amowry/WARBL2/warbl2_firmware/Battery_management.ino

/*
Notes:

The battery is a 400 mAH 2/3 AAA NiMH cell. Example brands are PKCell, Kastar, Dantona, and GP. Either flat top or button top works. The real-world capacity of these is usually around 350 mAH, and charging takes 3 hours.
The BQ25172 charger will charge safely without any of this code when enabled by driving the chargeEnable pin high. The code monitors the battery level and does a better job of charge termination (0 dV/dt algorithm) to prolong battery life.
The charger will only start charging if the battery voltage is below ~ 1.35V and the battery temperature is between ~ 0 and 40 degrees C.
Charging is set by resistors to ~110 mA (0.275 C) with a 4-hr safety timer. The charger will also terminate if battery voltage is > 1.7 V or battery temperature is over 40 degrees C.
Total device consumption is < 100 mA @ 5V, so any USB host (including iOS) will be able to charge.
The charger will report a fault (missing battery, out of temperature range) by blinking the STAT pin at 1 Hz.
*/

//#define PRINT_CHARGING_DATA  // For plotting voltage while charging


void manageBattery(bool send) {

    static byte chargingStatus = 0;          // 0 is not charging, 1 is charging, 2 is fault
    static byte prevChargingStatus = 0;      // Keep track of when it has changed.
    static byte tempChargingStatus;          // The assumed charging status before it has been finalized by waiting to detect a fault
    static byte prevTempChargingStatus = 0;  // Keep track of when it has changed.
    static bool chargeEnabled = false;       // Whether the charger is currently powered (by enabling the buck converter). The charger will then decide whether to charge, and report status on the STAT pin.
    static float voltageQueue[21];           // FIFO queue for finding the slope of the voltage curve while charging.
    static float voltageSlope;               // Change in smoothed voltage over the previous 10 minutes
    static unsigned long minuteTimer = 0;    // Resets every minute while charging to recalculate battery percentage.
    static bool chargeTerminated = false;    // Tells us that a charge cycle has been terminated because the cell is full.
    static byte flatSlopeCounts = 0;         // Tally of zero-slope readings (two are required to terminate charging).
    static bool statusChanged;               // Flag when the charging status has changed.
    unsigned long nowtime = millis();

    USBstatus = nrf_power_usbregstatus_vbusdet_get(NRF_POWER) + tud_ready();  // A combination of usbregstatus and tud_ready() can be used to detect battery power (0), dumb charger (1), or connected USB host (2).
    static byte prevUSBstatus;
    static unsigned long USBstatusChangeTimer;

    if (USBstatus != prevUSBstatus) {  // Keep track of when USB status changed, because we need to wait a bit for doing some things like enabling charging. USB power may be detected slightly before a USB host, causing us to briefly think there's a dumb charger.
        USBstatusChangeTimer = nowtime;
        prevUSBstatus = USBstatus;
    }

    // Check if we've been plugged in to power.
    if (battPower && USBstatus != BATTERY_POWER) {
        digitalWrite(powerEnable, LOW);  // Disable the boost converter if there is USB power. The device will then power down if USB is unplugged again.
        battPower = false;
        recordRuntime(false);  // Record how long we were under battery power.
    }


    smoothed_voltage = getBattVoltage();  // Read the battery


    // Detect charging status based on the STAT pin from the charger (off if charging, blinking if fault)
    if (!battPower) {  // Don't bother with any of this if we're not plugged in.

        // Monitor the STAT pin to tell if we're charging.
        if (digitalRead(STAT) == 0) {  // Charging
            pulseLED[RED_LED] = true;
            tempChargingStatus = 1;  // Provisionally change the status.
        } else {                     // Not charging
            pulseLED[RED_LED] = false;
            tempChargingStatus = 0;  // Provisionally change the status.
        }


        // Detect change in charging status
        if (prevTempChargingStatus != tempChargingStatus) {
            statusChanged = 1;
            if (communicationMode) {  // Send the status to the Config Tool if it has changed.
                sendMIDICouplet(MIDI_SEND_BATTERY_CHARGE_STATUS, tempChargingStatus);
            }
            prevTempChargingStatus = tempChargingStatus;
        }


        byte finalizeStatus = faultDetect(statusChanged);  // Watch for a blinking charger STAT pin, indicating a fault.
        statusChanged = 0;

        // Do nothing if finalizeStatus == 0 because there hasn't been a change or we haven't waited long enough to detect a fault.

        if (finalizeStatus == 1) {  // It's okay to accept the change in status.
            chargingStatus = tempChargingStatus;
        } else if (finalizeStatus == 2) {  // Fault
            chargingStatus = 2;
        }

        if (prevChargingStatus != chargingStatus) {
            if (chargingStatus == 1) {
                chargeStartTime = nowtime;  // Start a timer if we just started charging.
                minuteTimer = nowtime;
                for (byte i = 0; i < 21; i++) {  // Reset the readings in the voltage buffer to 0 in case there are readings in it from a previous charge cycle.
                    voltageQueue[i] = 0;
                }
                flatSlopeCounts = 0;  // Reset the number of zero-slope readings.
            }
            // Don't do anything if the charging status just changed to 0, because that means that charging was stopped by the charger, which should be rare (i.e. we missed termination and the safety timer ran down).

            prevChargingStatus = chargingStatus;

            sendMIDICouplet(MIDI_SEND_BATTERY_CHARGE_STATUS, chargingStatus);  // Send charging status again in case a fault was detected.
        }
    }




    // Estimate the battery percentage remaining via coulometry. This is a rough estimate and mostly meaningless before the first full charge because we don't know the initial state of the battery. It becomes still more accurate after the first full discharge.

    // If we're charging, every minute subtract the estimated added run time due to charging from the stored run time on the current charge (increasing the battery percentage as we're charging)
    if (chargingStatus == 1 && (nowtime - minuteTimer) > 60000) {
        prevRunTime = prevRunTime - (fullRunTime * 0.0055);  // Subtract the estimated run time added per one minute of charging.
        if (prevRunTime < 1) {
            prevRunTime = 1;  // Never go below 1.
        }

        minuteTimer = nowtime;
        static byte computeCycles = 0;
        computeCycles++;
        if (computeCycles == 5) {  // Every 5 minutes, update the recorded run time in EEPROM in case the power is cut. The EEPROM can handle more than 4 million write cycles, but don't do this too often. An EEPROM write also takes up to 5 ms.
            writeEEPROM(EEPROM_RUNTIME_START, highByte(prevRunTime));
            writeEEPROM(EEPROM_RUNTIME_START + 1, lowByte(prevRunTime));
            computeCycles = 0;
        }
    }




    // Calculate the current battery percentage based on the run time and the run time available from a full charge. Don't let it drop below 1% because if it's truly 0 it will shut down.
    unsigned long currentRun = (nowtime - runTimer) / 60000;  // Minutes we've been running since powerup

    if (!battPower) {  // Ignore time since powerup if we're plugged in.
        currentRun = 0;
    }
    battLevel = constrain(((fullRunTime - (prevRunTime + currentRun)) / float(fullRunTime)) * 100, 1, 100);  // Calculate percentage remaining.
    if ((prevRunTime + currentRun) > fullRunTime) {                                                          // If we've run longer than the expected total run time, just set the battery level to 1% until the voltage drops low enough to power down.
        battLevel = 1;
    }
    if (chargingStatus == 1 && battLevel > 98) {  // Don't let the percentage reach 100% while charging until there is a termination.
        battLevel = 98;
    }



    static byte cycles = 40;  // 40 cycles is 30 seconds.
    // Send voltage and charging status to Config Tool. This also tells the Config Tool to stay connected because it's the only message sent at a regular interval.
    if (cycles == 40 || send) {
        if (communicationMode) {
            sendMIDICouplet(MIDI_SEND_BATTERY_VOLTAGE, (((smoothed_voltage + 0.005) * 100) - 50));  // Convert to 0-127 for sending to Config Tool as 7 bits (possible range of 0.5 - 1.77 V in this format).
            sendMIDICouplet(MIDI_SEND_BATTERY_CHARGE_STATUS, chargingStatus);                       // Send charging status.
            sendMIDICouplet(MIDI_SEND_BATTERY_CHARGE_PERC, battLevel);                              // Send battery level.
        }
    }



    // If we're charging, try to detect a full cell earlier than the charger timeout by monitoring dV/dt.
    if (cycles == 40) {  // Every 30 seconds, record a new smoothed voltage reading, add it to the queue, and find the difference between the first and last reading in the queue.
        cycles = 0;

        if (chargingStatus == 1) {
            for (byte i = 0; i < 20; i++) {  // Shift a new smoothed voltage reading into the queue.
                voltageQueue[20 - i] = voltageQueue[(20 - i) - 1];
            }
            voltageQueue[0] = smoothed_voltage;

            // On rare occasions the battery voltage may suddenly jump up or down while charging. Currently undiagnosed-- it may be the charger or a change in battery load. The block below detects a sudden drop in voltage and adjusts previous measurements accordingly to prevent false termination.
            float voltageDrop = voltageQueue[1] - voltageQueue[0];
            if (voltageDrop > 0.002) {
                for (byte i = 1; i < 21; i++) {  // Adjust all previous measurements.
                    voltageQueue[i] = voltageQueue[i] - voltageDrop;
                }
                writeEEPROM(EEPROM_RESERVED_TESTING, readEEPROM(EEPROM_RESERVED_TESTING) + 1);  // Testing--record if there's been an adjustment
            }


            voltageSlope = voltageQueue[0] - voltageQueue[20];  // Find the difference in voltage over the past ten minutes (this number will be large and meaningless until 10 minutes has past and the queue has been populated--that's okay because we don't need to terminate in the first 10 minutes anyway).
            if (voltageSlope < 0.001) {                         // If the curve has been flat for the previous 10 minutes, increment the number of zero-slope readings.
                flatSlopeCounts++;
            }
            if (flatSlopeCounts >= 2) {           // If we've had two readings where the slope has been flat for the previous ten minutes, terminate charging.
                digitalWrite(chargeEnable, LOW);  // Disable charging.
                chargeEnabled = 0;
                chargeTerminated = 1;  // This tells us not to enable charging again until the power is cycled.
                //Serial.println("charge terminated by 0 dV");
                analogWrite(LEDpins[GREEN_LED], 1023);     // Indicate end of charge.
                writeEEPROM(EEPROM_RUNTIME_START, 0);      // Reset the total run time because we are now fully charged (high byte).
                writeEEPROM(EEPROM_RUNTIME_START + 1, 0);  // Low byte
                writeEEPROM(EEPROM_LOW_CHARGE, 3);         // Remember that there has been a termination.
                prevRunTime = 0;
                flatSlopeCounts = 0;
            }


#if defined(PRINT_CHARGING_DATA)
            Serial.print(smoothed_voltage, 3);
            Serial.print(",");
            Serial.print(voltageSlope, 3);
            Serial.print(",");
            Serial.println(readEEPROM(EEPROM_RESERVED_TESTING));
#endif
        }
    }

    if (!send) {  // Increment the counter if we haven't only come here to send data to the Config Tool.
        cycles++;
    }



    // Enable or disable charging (by supplying power to the charger with the buck converter) based on settings and whether USB power is available.
    // Make sure chargeEnable doesn't go high when there's no USB power because it may backpower the buck converter through the EN pin.
    if ((nowtime - USBstatusChangeTimer) > 2000 && !chargeTerminated && !chargeEnabled && ((WARBL2settings[CHARGE_FROM_HOST] && !battPower) || USBstatus == DUMB_CHARGER)) {
        digitalWrite(chargeEnable, HIGH);  // Enable charging (the charger will determine if it should actually start charging, based on batt voltage and temp.)
        chargeEnabled = 1;
        chargeStartTime = millis();
        writeEEPROM(EEPROM_RESERVED_TESTING, 0);
        if (prevRunTime > fullRunTime) {  // If we've run longer than expected on battery, make the run time the same as the expected run time when we start charging. This will allow the battery percentage to start increasing right away rather than being stuck at 1% for a while.
            prevRunTime = fullRunTime;
        }
    } else if (chargeEnabled && ((WARBL2settings[CHARGE_FROM_HOST] == 0 && USBstatus != DUMB_CHARGER) || battPower)) {  // Disable charging if we're on battery power or connected to a host and host charging isn't allowed.
        digitalWrite(chargeEnable, LOW);                                                                                // Disable charging.
        chargeEnabled = 0;
    }


    // Check to see if we've been idle long enough to power down.
    if (battPower && (nowtime - powerDownTimer > WARBL2settings[POWERDOWN_TIME] * 60000) && (WARBL2settings[POWERDOWN_TIME] < 25)) {
        powerDown(false);  // This line can be commented out to disable auto power off, for testing the battery.
    }


    // Shut down when the battery is low.
    if (nowtime > 2000 && battPower && smoothed_voltage <= 1.0) {  // Give some time to make sure we detect USB power if it's present.
        analogWrite(LEDpins[RED_LED], 1023);                       // Long red LED to indicate shutdown because of low battery
        delay(5000);
        powerDown(true);  // Power down and reset the total run time available on a full charge (because we have just measured it by using up a full charge). ToDo: Decide if the run time should only be reset if there hasn't been a partial charge during the run cycle. The run time will be a little less accurate if there have been partial charges since the last termination.
        //ToDo: The battery percentage needs to be reset to 0 when the voltage drops to 1.0.
    }
}







// Use a timer to delay response to changes in charging status while we try detect a charger fault (blinking STAT pin).
byte faultDetect(bool statusChanged) {

    static unsigned long faultTimer;
    static bool timing = false;
    static byte change = 0;
    byte ret;
    unsigned long nowtime = millis();

    if (statusChanged) {
        change++;                  // Count the number of times the charging status has changed.
        if (timing == false) {     // If this is the first time the function has been called
            faultTimer = nowtime;  // Start a timer
            timing = true;
        }
    }

    if ((nowtime - faultTimer) > 5000) {  // If we're timing and 5 seconds has past (The pin blinks at 1 Hz and this is called every 0.75 seconds, so we should detect a fault in 5 seconds if there is one.)...
        faultTimer = nowtime;
        timing = false;
        if (change < 2) {  // If the status has only changed once or not at all,
            ret = 1;       // finalize the current status.

            // If the status has changed more than once in 5 seconds, the pin is blinking and it's a fault.
        } else if ((nowtime - chargeStartTime) > 10000) {  //Don't allow a fault for several seconds after the start of charging. Otherwise rapid toggling of the "Charge from USB Hosts" might trigger a fault.
            ret = 2;
        }
        change = 0;
    } else ret = 0;  // Keep waiting to finalize the current status.
    return ret;
}







void powerDown(bool resetTotalRuntime) {

    if (battPower) {
        recordRuntime(resetTotalRuntime);
        analogWrite(LEDpins[RED_LED], 1023);  // Indicate power down.
        delay(500);
        analogWrite(powerEnable, 0);  // Disable the boost converter to cut power to the entire device.
    }
}







// Record how long we've been running on battery power.
void recordRuntime(bool resetTotalRuntime) {

    runTimer = (millis() - runTimer) / 60000;  // Calculate how many minutes we have been powered by the battery.

    runTimer = runTimer + prevRunTime;  // Rebuild stored run time.

    if (resetTotalRuntime) {                       // Use the elapsed run time to update the total run time available on a full charge, because we have terminated because of a low battery.
        if (readEEPROM(EEPROM_LOW_CHARGE) == 3) {  // If we haven't already recorded the total run time
            writeEEPROM(EEPROM_EST_RUNTIME_START, highByte(runTimer));
            writeEEPROM(EEPROM_EST_RUNTIME_START + 1, lowByte(runTimer));
            writeEEPROM(EEPROM_LOW_CHARGE, 1);  // Record that we've done this so we won't do it again until there has been another full charge.
        }
    }

    writeEEPROM(EEPROM_RUNTIME_START, highByte(runTimer));  // Update the recorded run time in EEPROM.
    writeEEPROM(EEPROM_RUNTIME_START + 1, lowByte(runTimer));
}








float getBattVoltage() {

    // Read battery voltage
    analogReference(AR_INTERNAL_1_8);          // Use 1.8 V reference to maximize resolution. The battery should never read higher than ~1.7 V because that's the charger overvoltage cutoff.
    digitalWrite(battReadEnable, HIGH);        // We only connect the battery to the pin when reading to make sure it's not connected when the MCU is powered down.
    analogOversampling(1);                     // Minimal oversampling for the throwaway read
    analogRead(battRead);                      // Dummy read to settle the reference
    analogOversampling(64);                    // Increase oversampling for precise 12-bit reading.
    float battReading = analogRead(battRead);  // 290 uS.
    digitalWrite(battReadEnable, LOW);
    analogReference(AR_VDD4);  // Change back to VDD reference for reading pressure sensor.
    analogOversampling(8);     // Change back to 8X oversampling for reading pressure sensor.

    // Calculate voltage. Assumes 12-bit ADC and 1.8V ref
    battReading = (battReading * 0.439453125f) / 1000;  // mV

    const float alpha = 0.05f;  // Time constant can be tweaked.
    static float smoothed_voltage = battReading;
    smoothed_voltage = (1.0 - alpha) * smoothed_voltage + alpha * battReading;  // Exponential moving average

    return smoothed_voltage;
}
