amowry/WARBL2/warbl2_firmware/Functions.ino

#include "Defines.h"


// Debug
void printStuff(void) {

    //Serial.println(sensorValue);
    //Serial.println(twelveBitPressure);
    //Serial.println(smoothed_pressure);
    //Serial.println("");

    //Serial.println(readEEPROM(EEPROM_HARDWARE_VERSION));

    /*
    for (byte i = 0; i < 9; i++) {
        Serial.println(toneholeRead[i]);
    }
     Serial.println("");
*/

    //static float CPUtemp = readCPUTemperature(); // If needed for something like calibrating sensors. There are also temp sensors on the IMU, magnetometer (if installed), and both BMP sensors (if installed).

    //This can be used to print out the currently selected fingering chart (all 256 possible values) when button 1 is clicked.
    /*
    if (digitalRead(4) == 0) {
        for (unsigned int i = 0; i < 256; i++) {
            Serial.print(getNote(i << 1));
            Serial.print(" ");
        }
        delay(5000);
    } 
*/

    // Print the total minutes run time per charge (for estimating battery health).
    /*
         int runTimePerCharge;
         getEEPROM(EEPROM_EST_RUNTIME_START, runTimePerCharge);
         Serial.println(runTimePerCharge);
         */
}









// Determine how long to sleep each time through the loop.
byte calculateDelayTime(void) {

    byte delayCorrection = (millis() - wakeTime);  // Include a correction factor to reduce jitter if something else in the loop or the radio interrupt has eaten some time.
                                                   // The main thing that adds jitter to the loop is sending lots of data over BLE, i.e. pitchbend, CC, etc. (though it's typically not noticeable). Being connected to the Config Tool is also a significant source of jitter.
                                                   // With USB MIDI only there is virtually no jitter with a loop period of 2 ms.
    //if (delayCorrection > 3) { Serial.println(delayCorrection); }  // Print the amount of time that other things have consumed.

    byte delayTime = 3;

    if (connIntvl == 0) {  // Use a 2 ms sleep instead if we are only using USB MIDI.
        delayTime = 2;
    }

    if (delayCorrection < delayTime) {  // If we haven't used up too much time since the last time through the loop, we can sleep for a bit.
        delayTime = delayTime - delayCorrection;
        return delayTime;
    }
    return 0;
}









#ifdef PROTOTYPE46
// This version needed for the few early prototypes out there
// Read the pressure sensor and get latest tone hole readings from the ATmega.
void getSensors(void) {

    analogPressure.update();  //  Read the pressure sensor now while the ATmega is still asleep and the board is very quiet.
    twelveBitPressure = analogPressure.getRawValue();
    smoothed_pressure = analogPressure.getValue();  // Use an adaptively smoothed 12-bit reading to map to CC, aftertouch, poly.
    sensorValue = twelveBitPressure >> 2;           // Reduce the reading to stable 10 bits for state machine.


    // Receive tone hole readings from ATmega32U4. The transfer takes ~ 125 us.
    byte toneholePacked[] = { 0, 0, 0, 0, 0, 0, 0, 0, 0, 0, 0, 0 };
    SPI.beginTransaction(SPISettings(2000000, MSBFIRST, SPI_MODE0));
    digitalWrite(2, LOW);   // CS -- Wake up ATmega.
    delayMicroseconds(10);  // Give it time to wake up.
    SPI.transfer(0);        // We don't receive anything useful back from the first transfer.
    for (byte i = 0; i < 12; i++) {
        toneholePacked[i] = SPI.transfer(i + 1);
    }
    digitalWrite(2, HIGH);  //CS
    SPI.endTransaction();

    // Unpack the readings from bytes to ints.
    for (byte i = 0; i < 9; i++) {
        toneholeRead[i] = toneholePacked[i];  // Unpack lower 8 bits.
    }

    for (byte i = 0; i < 4; i++) {  // Unpack the upper 2 bits of holes 0-3.
        toneholePacked[9] = toneholePacked[9] & 0b11111111, BIN;
        toneholeRead[i] = toneholeRead[i] | (toneholePacked[9] << 2) & 0b1100000000;
        toneholePacked[9] = toneholePacked[9] << 2;
    }

    for (byte i = 4; i < 8; i++) {  // Unpack the upper 2 bits of holes 4-7.
        toneholePacked[10] = toneholePacked[10] & 0b11111111, BIN;
        toneholeRead[i] = toneholeRead[i] | (toneholePacked[10] << 2) & 0b1100000000;
        toneholePacked[10] = toneholePacked[10] << 2;
    }

    toneholeRead[8] = toneholeRead[8] | (toneholePacked[11] << 8);  // Unpack the upper 2 bits of hole 8.



    for (byte i = 0; i < 9; i++) {
        // run through adaptive smoothing filter
        filterToneholes[i].update(toneholeRead[i]);
        toneholeRead[i] = filterToneholes[i].getValue();

        if (calibration == 0) {  // If we're not calibrating, compensate for baseline sensor offset (the stored sensor reading with the hole completely uncovered).
            toneholeRead[i] = toneholeRead[i] - toneholeBaseline[i];
        }
        if (toneholeRead[i] < 0) {  // In rare cases the adjusted readings might end up being negative.
            toneholeRead[i] = 0;
        }
    }
}


#else

void getSensors(void) {

    if (!useBMP) {                // Honeywell ABPLLND060MGAA3 pressure sensor (older)
        analogPressure.update();  //  Read the pressure sensor now while the ATmega is still asleep and the board is very quiet.
        twelveBitPressure = analogPressure.getRawValue();
        smoothed_pressure = analogPressure.getValue();  // Use an adaptively smoothed 12-bit reading to map to CC, aftertouch, poly.
        sensorValue = twelveBitPressure >> 2;           // Reduce the reading to stable 10 bits for state machine.
    }

    else {                                                                           // Bosch BMP585 preessure sensor (newer).
                                                                                     // This sensor has less noise, so we could probably use one more effective bit for the pressure mapping calculations. It also has potential for inhale notes/mapping and has a much higher range than the Honeywell sensor.
        if (bmp.performReading()) {                                                  // SPI transfer takes 58 us at 8 MHz (~same as reading older analog sensor).
            twelveBitPressure = (((bmp.pressure - BMPcalibration) * 54.60f) + 400);  // Scale to ABPLLND060MGAA3 equivalent range at twelve bits.
            sensorValue = twelveBitPressure >> 2;                                    // Reduce the reading to stable 10 bits for state machine.
            analogPressure.update(twelveBitPressure);                                // Update the smoothing filter.
            smoothed_pressure = analogPressure.getValue();                           // Use an adaptively smoothed 12-bit reading to map to CC, aftertouch, poly. The filter currently constrains the values 0-4095 because of the adc bits used in setup. I don't think the library will accept negative values.
        }
    }


    // Receive tone hole readings from ATmega32U4.
    byte toneholePacked[] = { 0, 0, 0, 0, 0, 0, 0, 0, 0, 0, 0, 0 };

    SPI.beginTransaction(SPISettings(2000000, MSBFIRST, SPI_MODE0));
    digitalWrite(2, LOW);
    delayMicroseconds(15);  // Give the ATmega time to wake up and preload the test byte into the buffer.

    byte testByte = SPI.transfer(0);  // The first byte received is for verification of SPI alignment. It should be 0xff. This tests whether the ATmega was ready at the start of the transfer.
    bool goodtestByte = (testByte == 0xff);

    for (byte i = 0; i < 11; i++) {
        toneholePacked[i] = SPI.transfer(i + 1);
    }
    toneholePacked[11] = SPI.transfer(useBellSensor + 20);  // The final transfer is dual purpose-- receive the last byte and send the bell sensor state.

    digitalWrite(2, HIGH);
    SPI.endTransaction();

    // Checksum to validate the sensor readings.
    uint8_t receivedChecksum = (toneholePacked[11] >> 4) & 0x0F;
    uint8_t computedChecksum = computeToneholeChecksum4(toneholePacked);

    bool goodChecksum = (receivedChecksum == computedChecksum);


    //if (!goodChecksum) {  // Indicate a bad transfer.
    //blinkNumber[RED_LED] = 1;
    //}


    if (goodChecksum && goodtestByte) {  // Just try again next time if the transfer was bad. This happens occasionally if lots of MIDI messages are being sent.
                                         //...could be AHB bus stall issue: https://devzone.nordicsemi.com/f/nordic-q-a/127744/ble-radio-interrupts-interfering-with-spi
                                         // ...or one of the many issues with SPIM3. SPIM2 seems to be similar, though. You can select either by changing the build flag in boards.local.txt. 0 is for SPIM3, 1 for SPIM2.


        // Unpack the readings from bytes to ints.
        for (byte i = 0; i < 9; i++) {
            toneholeRead[i] = toneholePacked[i];
        }

        byte b9 = toneholePacked[9];
        byte b10 = toneholePacked[10];

        for (byte i = 0; i < 4; i++) {
            toneholeRead[i] |= ((b9 << 2) & 0b1100000000);
            b9 <<= 2;
        }

        for (byte i = 4; i < 8; i++) {
            toneholeRead[i] |= ((b10 << 2) & 0b1100000000);
            b10 <<= 2;
        }

        toneholeRead[8] |= ((toneholePacked[11] & 0x03) << 8);


        for (byte i = 0; i < 9; i++) {
            // Run through adaptive smoothing filter. Takes 50 us.
            filterToneholes[i].update(toneholeRead[i]);
            toneholeRead[i] = filterToneholes[i].getValue();

            if (calibration == 0) {  // If we're not calibrating, compensate for baseline sensor offset (the stored sensor reading with the hole completely uncovered).
                toneholeRead[i] = toneholeRead[i] - toneholeBaseline[i];
            }
            if (toneholeRead[i] < 0) {  // In rare cases the adjusted readings might end up being negative.
                toneholeRead[i] = 0;
            }
        }
    }
}

#endif








// If using the BMP pressure sensors, adjust for ambient pressure.
void readAmbientPressure() {
    if (bmpAmbient.performReading()) {
        BMPcalibration = bmpAmbient.pressure + BMPoffset;  //Calibrate to ambient, adding the initial offset between the two sensors at startup.
    }
    checkForBreathPause();  // See if there's currently no breath pressure, to adjust calibration if necessary.
}









// If using the BMP sensors, the breath and ambient sensors can drift apart very slightly because of physical PCB stress if the temperature changes rapidly.
// Here we detect if there's currently no breath pressure, in which case we can reset the sensor offset to adjust for drift if necessary.
void checkForBreathPause() {
    constexpr size_t WINDOW_SAMPLES = 60;  // 3-second window at 20Hz.
    static float buf[WINDOW_SAMPLES] = {};
    static size_t idx = 0;
    static bool filled = false;
    const byte resetRange = 6;  // Number of counts away from 400 within which we may reset ambient pressure. By keeping this low we help avoid spurious resets.

    buf[idx] = twelveBitPressure;  // Use a ring buffer to track the range in pressure over the time window.
    idx = (idx + 1) % WINDOW_SAMPLES;
    if (idx == 0) filled = true;

    size_t count = filled ? WINDOW_SAMPLES : (idx == 0 ? WINDOW_SAMPLES : idx);

    float mn = buf[0], mx = buf[0];
    for (size_t i = 1; i < count; i++) {
        mn = min(mn, buf[i]);
        mx = max(mx, buf[i]);
    }
    float range = mx - mn;

    if (filled && range < 3 && ABS(400 - twelveBitPressure) < resetRange) {
        BMPoffset = bmp.pressure - bmpAmbient.pressure;  // Reset the sensor offset if the pressure range over the time window is low and the breath pressure is close to 400 (the calibration pressure at startup). If these conditions are met we assume the user isn't blowing.
        idx = 0;
        filled = false;  // Don't let the window trigger again until it's refilled.
        Serial.println("reset");
    }
}








// Calculate checksum for received sensor values. It should be ~94% effective at detecting a bad sensor value.
uint8_t computeToneholeChecksum4(const uint8_t* p) {
    uint8_t x = 0;

    for (uint8_t i = 0; i < 11; i++) {
        x ^= p[i];
    }

    x ^= (p[11] & 0x03);

    x ^= (x >> 4);
    return x & 0x0F;
}









void readIMU(void) {

    // Note: Gyro is turned off by default to save power unless using roll/pitch/yaw, elevation register, or sticks mode (see loadPrefs()).

    sensors_event_t accel;
    sensors_event_t gyro;
    sensors_event_t temp;
    sox.getEvent(&accel, &gyro, &temp);

    rawGyroX = gyro.gyro.x;
    rawGyroY = gyro.gyro.y;
    rawGyroZ = gyro.gyro.z;
    accelX = accel.acceleration.x;
    accelY = accel.acceleration.y;
    accelZ = accel.acceleration.z;
    IMUtemp = temp.temperature;

    // Calibrate gyro
    gyroX = rawGyroX - gyroXCalibration;
    gyroY = rawGyroY - gyroYCalibration;
    gyroZ = rawGyroZ - gyroZCalibration;

    float deltat = IMUdeltatUpdate();

    sfusion.MahonyUpdate(gyroX, gyroY, gyroZ, accelX, accelY, accelZ, deltat);

    // Pitch and roll are swapped due to PCB sensor orientation.
    roll = sfusion.getPitchRadians();
    pitch = sfusion.getRollRadians();

    float* quat = sfusion.getQuat();

    float qw = quat[0];
    float qx = quat[1];
    float qy = quat[2];
    float qz = quat[3];

    // Gravity vector in the body's local frame (based on standard Z-down or Z-up)
    // Here, we assume Z is pointing down in the global frame
    float pvx = 2.0f * (qx * qz - qw * qy);
    float pvy = 2.0f * (qw * qx + qy * qz);
    float pvz = qw * qw - qx * qx - qy * qy + qz * qz;

    // Calculate unconstrained pitch in the local frame (rotation about the body's Y-axis) (is our roll due to chip orientation)
    float localroll = atan2f(pvx, pvz);


    // Adjust pitch so it makes more sense for way warbl is held, shift it 180 deg
    pitch += PI;
    if (pitch > PI) pitch -= TWO_PI;


    // adjust localroll
    localroll -= PI;
    if (localroll > PI) localroll -= TWO_PI;
    if (localroll < -PI) localroll += TWO_PI;
    localroll *= -RAD_TO_DEG;

    // use it
    roll = localroll;

    // Invert
    pitch = -pitch;
    pitch = pitch * RAD_TO_DEG;

    const float abspitch = abs(pitch);

    static float runningRoll = roll;
    float gyro_roll = gyroY * deltat * RAD_TO_DEG;

    // the normal roll is really good now, except for when the warbl is nearly on its end, where we use the gyro based roll only
    // filter the transitions
    const float alpha = abspitch < 75.0f ? 1.0f : abspitch < 80.0f ? (80.0f - abspitch) * 0.2f
                                                                   : 0.0f;

    runningRoll = (1.0f - alpha) * (runningRoll + gyro_roll) + (alpha * roll);

    while (runningRoll >= 270) {  // Wrap
        runningRoll -= 360;
    }
    while (runningRoll <= -270) {
        runningRoll += 360;
    }

    roll = runningRoll;

    // Compute compass heading of the long axis of the WARBL because it is independent of the "local" roll.

    static bool axisHeadingInitialized = false;

    // World-frame direction of body +Y axis (WARBL long axis)
    float vx = 2.0f * (qx * qy - qw * qz);
    float vy = 1.0f - 2.0f * (qx * qx + qz * qz);
    float vz = 2.0f * (qy * qz + qw * qx);

    // Don't calculate heading if the WARBL is too close to vertical.
    // In that case, keep the previous valid heading.
    //     - JLC: this is not a clean transition, perhaps fade into using real yaw?
    const float maxAbsVz = 0.995f;

    if (fabsf(vz) < maxAbsVz) {
        axisHeading = atan2f(vx, vy) * RAD_TO_DEG;

        while (axisHeading > 180.0f) axisHeading -= 360.0f;
        while (axisHeading < -180.0f) axisHeading += 360.0f;

        currAxisHeading = axisHeading;  // Save raw heading for recentering

        axisHeading += axisHeadingOffset;

        while (axisHeading > 180.0f) axisHeading -= 360.0f;
        while (axisHeading < -180.0f) axisHeading += 360.0f;

        axisHeadingInitialized = true;
    } else if (!axisHeadingInitialized) {
        axisHeading = 0.0f;
        currAxisHeading = 0.0f;
    }



    // Drumstick mode: WARBL2 must be held by the USB end, with the button side up. No note-off messages are sent.
    // This mode is "hidden" -- to turn it on select "-18" in the transpose menu and then click "Auto-caibrate bell sensor only" within 10 seconds.
    if (IMUsettings[preset][STICKS_MODE]) {
        static bool armed = 0;
        static float maxGyro;
        static byte LEDCounter = 0;  // Time how long the LED is on.

        if (LEDCounter > 0) {  // Count up if the LED is on.
            LEDCounter++;
        };

        if (LEDCounter > 5) {  // Turn off LED after a bit.
            analogWrite(LEDpins[GREEN_LED], 0);
            analogWrite(LEDpins[BLUE_LED], 0);

            LEDCounter = 0;
        }

        if (gyroX > 0.5f) {
            armed = true;                              // Detect forward rotation above a threshold to prepare for a hit.
            if (gyroX > maxGyro) { maxGyro = gyroX; }  // Find the fastest X rotation, to use for hit velocity.
            else if (maxGyro > 0) {
                maxGyro -= 0.7f;  // Gradually reduce the velocity analog if the rotation is slowing. This adjusts the velocity and/or prevents a hit if you start out with a fast swing but then slow it before the rebound occurs.
            }
            if (maxGyro <= 0) {
                armed = false;
            }
        }
        if (gyroX < 0 && armed == true) {                                    // A hit occurs if we are armed and the X gyro goes negative (indicating a slight rebound).
            byte hitVelocity = 12 * (constrain(maxGyro + 1, 1.0f, 10.58f));  // Scale the velocity up to 0-127.
                                                                             // Just in case
            sendMIDI(NOTE_ON, mainMidiChannel, yawOutput, hitVelocity);      // Use yawOutput for MIDI note.
            analogWrite(LEDpins[GREEN_LED], hitVelocity << 3);               // Fire teal LED to indicate a hit, with brightness based on note velocity.
            analogWrite(LEDpins[BLUE_LED], hitVelocity << 1);
            LEDCounter = 1;  // Start counting to turn the LED off again.
            armed = false;   // Don't allow another hit until we've passed the threshold again.
            maxGyro = 0;
            powerDownTimer = pitchBendTimer;  // Reset the powerDown timer because we're sending notes.
        }
    }
}










// Calculate deltat for the IMU. Using the RTC2 timer because it is more accurate than micros() during a period of sleep. 30.5 us resolution.
float IMUdeltatUpdate() {
    static uint32_t lastUpdate = 0;
    uint32_t now = NRF_RTC2->COUNTER;
    uint32_t elapsed = (now - lastUpdate) & 0xFFFFFF;  // 24-bit counter
    lastUpdate = now;
    float delta = elapsed / 32768.0f;
    delta = constrain(delta, 0.001f, 0.02f);
    return delta;
}










// Calibrate the gyroscope when the command is received from the Config Tool.
void calibrateIMU(bool reset = false) {

    if (!reset) {
        sox.setGyroDataRate(LSM6DS_RATE_208_HZ);  // Make sure the gyro is on.
        delay(50);                                // Give it a bit of time.
        readIMU();                                // Get a reading in case we haven't been reading it.
        delay(50);                                // Give it a bit of time.
        readIMU();                                // Another reading seems to be necessary after turning the gyro on.

        gyroXCalibration = rawGyroX;
        gyroYCalibration = rawGyroY;
        gyroZCalibration = rawGyroZ;
    } else {
        // reset
        gyroXCalibration = gyroYCalibration = gyroZCalibration = 0.0;
    }

    putEEPROM(EEPROM_XGYRO_CALIB_START, gyroXCalibration);  // Put the current readings into EEPROM.
    putEEPROM(EEPROM_YGYRO_CALIB_START, gyroYCalibration);
    putEEPROM(EEPROM_ZGYRO_CALIB_START, gyroZCalibration);
    writeEEPROM(EEPROM_XGYRO_CALIB_SAVED, reset ? 0 : 3);  // Remember that we have saved a calibration.
}









// Reset heading 0 to current heading
void centerIMU() {
    yawOffset = -currYaw;
    axisHeadingOffset = -currAxisHeading;
}









// Map IMU to CC and send
void sendIMU() {

    static byte prevRollCC = 0;
    static byte prevPitchCC = 0;
    static byte prevYawCC = 0;

    // The min and max settings from the Config Tool range from 0-36 and are scaled up to the maximum range of angles for each DOF.

    if (IMUsettings[preset][SEND_ROLL]) {

        byte lowerConstraint;
        byte upperConstraint;

        if (IMUsettings[preset][ROLL_OUTPUT_MIN] > IMUsettings[preset][ROLL_OUTPUT_MAX]) {  // Flip the constraints if the lower output is greater than the upper output, so the output can be inverted.
            lowerConstraint = IMUsettings[preset][ROLL_OUTPUT_MAX];
            upperConstraint = IMUsettings[preset][ROLL_OUTPUT_MIN];
        }

        else {
            lowerConstraint = IMUsettings[preset][ROLL_OUTPUT_MIN];
            upperConstraint = IMUsettings[preset][ROLL_OUTPUT_MAX];
        }

        byte rollOutput = constrain(map((roll + 90) * 1000, IMUsettings[preset][ROLL_INPUT_MIN] * 5000, IMUsettings[preset][ROLL_INPUT_MAX] * 5000, IMUsettings[preset][ROLL_OUTPUT_MIN], IMUsettings[preset][ROLL_OUTPUT_MAX]), lowerConstraint, upperConstraint);

        if (prevRollCC != rollOutput) {
            sendMIDI(CONTROL_CHANGE, IMUsettings[preset][ROLL_CC_CHANNEL], IMUsettings[preset][ROLL_CC_NUMBER], rollOutput);
            prevRollCC = rollOutput;
        }
    }



    if (IMUsettings[preset][SEND_PITCH]) {

        byte lowerConstraint;
        byte upperConstraint;

        if (IMUsettings[preset][PITCH_OUTPUT_MIN] > IMUsettings[preset][PITCH_OUTPUT_MAX]) {  // Flip the constraints if the lower output is greater than the upper output, so the output can be inverted.
            lowerConstraint = IMUsettings[preset][PITCH_OUTPUT_MAX];
            upperConstraint = IMUsettings[preset][PITCH_OUTPUT_MIN];
        }

        else {
            lowerConstraint = IMUsettings[preset][PITCH_OUTPUT_MIN];
            upperConstraint = IMUsettings[preset][PITCH_OUTPUT_MAX];
        }

        byte pitchOutput = constrain(map((pitch + 90) * 1000, IMUsettings[preset][PITCH_INPUT_MIN] * 5000, IMUsettings[preset][PITCH_INPUT_MAX] * 5000, IMUsettings[preset][PITCH_OUTPUT_MIN], IMUsettings[preset][PITCH_OUTPUT_MAX]), lowerConstraint, upperConstraint);

        if (prevPitchCC != pitchOutput) {
            sendMIDI(CONTROL_CHANGE, IMUsettings[preset][PITCH_CC_CHANNEL], IMUsettings[preset][PITCH_CC_NUMBER], pitchOutput);
            prevPitchCC = pitchOutput;
        }
    }



    if (IMUsettings[preset][SEND_YAW] || IMUsettings[preset][STICKS_MODE]) {

        byte lowerConstraint;
        byte upperConstraint;

        if (IMUsettings[preset][YAW_OUTPUT_MIN] > IMUsettings[preset][YAW_OUTPUT_MAX]) {  // Flip the constraints if the lower output is greater than the upper output, so the output can be inverted.
            lowerConstraint = IMUsettings[preset][YAW_OUTPUT_MAX];
            upperConstraint = IMUsettings[preset][YAW_OUTPUT_MIN];
        }

        else {
            lowerConstraint = IMUsettings[preset][YAW_OUTPUT_MIN];
            upperConstraint = IMUsettings[preset][YAW_OUTPUT_MAX];
        }

        // Changed by AM 3/26 to use compass direction (axisHeading) rather than yaw.
        yawOutput = constrain(map((axisHeading + 180) * 1000, IMUsettings[preset][YAW_INPUT_MIN] * 10000, IMUsettings[preset][YAW_INPUT_MAX] * 10000, IMUsettings[preset][YAW_OUTPUT_MIN], IMUsettings[preset][YAW_OUTPUT_MAX]), lowerConstraint, upperConstraint);

        if (prevYawCC != yawOutput && IMUsettings[preset][SEND_YAW]) {
            sendMIDI(CONTROL_CHANGE, IMUsettings[preset][YAW_CC_CHANNEL], IMUsettings[preset][YAW_CC_NUMBER], yawOutput);
            prevYawCC = yawOutput;
        }
    }
}









// Use the Y accelerometer axis with gravity removed for vibrato.
void shakeForVibrato() {

    static float accelFilteredOld;
    const float timeConstant = 0.1f;
    float accelFiltered = timeConstant * accelY + (1.0f - timeConstant) * accelFilteredOld;  // Low-pass filter to isolate gravity from the Y accelerometer axis.
    accelFilteredOld = accelFiltered;
    float highPassY = accelY - accelFiltered;  // Subtract gravity to high-pass Y.

    static float accelFilteredBOld;
    const float timeConstant2 = 0.5f;
    float accelFilteredB = timeConstant2 * highPassY + (1.0f - timeConstant2) * accelFilteredBOld;  // A second low pass filter to minimize spikes from tapping the tone holes.
    float lastFilteredB = accelFilteredBOld;
    accelFilteredBOld = accelFilteredB;

    //accelFilteredB = highPassY;  // (Don't) temporarily eliminate this lowpass to see if speeds up response noticeably.

    const float shakeBendDepth = 4.0f * IMUsettings[preset][Y_PITCHBEND_DEPTH] / 100.0f;                   // Adjust the vibrato depth range based on the Config Tool setting.
    const float shakeModCCDepth = 64.0f * IMUsettings[preset][Y_SHAKE_MOD_CC_DEPTH] / 100.0f;              // Adjust the pressure CC out depth range based on the Config Tool setting.
    const float shakeModChanPressDepth = 64.0f * IMUsettings[preset][Y_SHAKE_MOD_CHPRESS_DEPTH] / 100.0f;  // Adjust the pressure ChanPress out depth range based on the Config Tool setting.
    const float shakeModKeyPressDepth = 64.0f * IMUsettings[preset][Y_SHAKE_MOD_KEYPRESS_DEPTH] / 100.0f;  // Adjust the pressure KeyPress out depth range based on the Config Tool setting.
    const float kShakeStartThresh = 0.5f;
    const float kShakeFinishThresh = 0.35f;
    const long kShakeFinishTimeMs = 400;
    const long ktapFilterTimeMs = 12;  // ms window for further filtering out taps on the tone holes
    static bool shakeActive = false;
    static bool tapFilterActive = false;
    static long lastThreshExceedTime = 0;
    static long tapFilterStartTime = 0;
    static bool preTrigger = false;
    const float kShakeGestureThresh = 20.0f;  // Theshold for shake gesture
    unsigned long nowtime = millis();


    if (abs(accelFilteredB) > kShakeGestureThresh) {  // This is for the shake gesture "button" assignment.
        shakeDetected = true;
    } else {
        shakeDetected = false;
    }

    bool doShake = (IMUsettings[preset][Y_SHAKE_PITCHBEND] || IMUsettings[preset][Y_SHAKE_MOD_CC] || IMUsettings[preset][Y_SHAKE_MOD_CHPRESS] || IMUsettings[preset][Y_SHAKE_MOD_KEYPRESS]);
    if (doShake) {  // Do this part only if one of the shake mod options is turned on.

        shakeVibrato = 0;
        shakePressureCCMod = 0;
        shakePressureChanPressMod = 0;
        shakePressureKeyPressMod = 0;

        if (tapFilterActive == false && abs(accelFilteredB) > kShakeStartThresh) {
            tapFilterActive = true;
            tapFilterStartTime = nowtime;
        }

        if ((nowtime - tapFilterStartTime) < ktapFilterTimeMs) {  // Return if we haven't waited long enough after crossing the shake threshold, for further filtering brief tone hole taps.
            return;
        }

        if (!preTrigger && abs(accelFilteredB) > kShakeStartThresh) {
            preTrigger = true;
        }

        if (!shakeActive && preTrigger  // Start shake vib only when doing a zero crossing after threshold has been triggered.
            // Comment out next line to test without the zero crossing requirement
            //&& ((lastFilteredB <= 0.0f && accelFilteredB > 0.0f) || (lastFilteredB > 0.0f && accelFilteredB <= 0.0f))
        ) {
            shakeActive = true;
            lastThreshExceedTime = nowtime;
            // Serial.println("Start ShakeVib");
        } else if (abs(accelFilteredB) > kShakeFinishThresh) {
            lastThreshExceedTime = nowtime;
        }

        if ((shakeActive || tapFilterActive) && (nowtime - lastThreshExceedTime) > kShakeFinishTimeMs) {
            // Stop shake vibrato.
            shakeActive = false;
            tapFilterActive = false;
            preTrigger = false;
        }


        if (shakeActive) {  // Normalize and clip, +/-15 input seems to be reasonably realistic max accel while still having it in the mouth!
            const float basenormshake = constrain(accelFilteredB * 0.06666f, -1.0f, 1.0f);
            float normshake = basenormshake;

            if (IMUsettings[preset][Y_PITCHBEND_MODE] == Y_PITCHBEND_MODE_UPDOWN) {
                normshake *= -1.0f;  // reverse phase
            } else if (IMUsettings[preset][Y_PITCHBEND_MODE] == Y_PITCHBEND_MODE_DOWNONLY) {
                normshake = constrain(normshake, -1.0f, 0.0f);
            } else if (IMUsettings[preset][Y_PITCHBEND_MODE] == Y_PITCHBEND_MODE_UPONLY) {
                normshake = constrain(-1.0f * normshake, 0.0f, 1.0f);
            } else if (IMUsettings[preset][Y_PITCHBEND_MODE] == Y_PITCHBEND_MODE_DOWNONLY_INV) {
                normshake = constrain(-1.0f * normshake, -1.0f, 0.0f);
            } else if (IMUsettings[preset][Y_PITCHBEND_MODE] == Y_PITCHBEND_MODE_UPONLY_INV) {
                normshake = constrain(normshake, 0.0f, 1.0f);
            }

            if (IMUsettings[preset][Y_SHAKE_PITCHBEND]) {
                shakeVibrato = (int)(normshake * shakeBendDepth * pitchBendPerSemi);
            }

            if (IMUsettings[preset][Y_SHAKE_MOD_CC]) {
                float normmodshake = basenormshake;
                if (IMUsettings[preset][Y_SHAKE_MOD_CC_MODE] == Y_PITCHBEND_MODE_UPDOWN) {
                    normmodshake *= -1.0f;  // reverse phase
                } else if (IMUsettings[preset][Y_SHAKE_MOD_CC_MODE] == Y_PITCHBEND_MODE_DOWNONLY) {
                    normmodshake = constrain(normmodshake, -1.0f, 0.0f);
                } else if (IMUsettings[preset][Y_SHAKE_MOD_CC_MODE] == Y_PITCHBEND_MODE_UPONLY) {
                    normmodshake = constrain(-1.0f * normmodshake, 0.0f, 1.0f);
                } else if (IMUsettings[preset][Y_SHAKE_MOD_CC_MODE] == Y_PITCHBEND_MODE_DOWNONLY_INV) {
                    normmodshake = constrain(-1.0f * normmodshake, -1.0f, 0.0f);
                } else if (IMUsettings[preset][Y_SHAKE_MOD_CC_MODE] == Y_PITCHBEND_MODE_UPONLY_INV) {
                    normmodshake = constrain(normmodshake, 0.0f, 1.0f);
                }
                shakePressureCCMod = (int)(normmodshake * shakeModCCDepth);
            }
            if (IMUsettings[preset][Y_SHAKE_MOD_CHPRESS]) {
                float normmodshake = basenormshake;
                if (IMUsettings[preset][Y_SHAKE_MOD_CHPRESS_MODE] == Y_PITCHBEND_MODE_UPDOWN) {
                    normmodshake *= -1.0f;  // reverse phase
                } else if (IMUsettings[preset][Y_SHAKE_MOD_CHPRESS_MODE] == Y_PITCHBEND_MODE_DOWNONLY) {
                    normmodshake = constrain(normmodshake, -1.0f, 0.0f);
                } else if (IMUsettings[preset][Y_SHAKE_MOD_CHPRESS_MODE] == Y_PITCHBEND_MODE_UPONLY) {
                    normmodshake = constrain(-1.0f * normmodshake, 0.0f, 1.0f);
                } else if (IMUsettings[preset][Y_SHAKE_MOD_CHPRESS_MODE] == Y_PITCHBEND_MODE_DOWNONLY_INV) {
                    normmodshake = constrain(-1.0f * normmodshake, -1.0f, 0.0f);
                } else if (IMUsettings[preset][Y_SHAKE_MOD_CHPRESS_MODE] == Y_PITCHBEND_MODE_UPONLY_INV) {
                    normmodshake = constrain(normmodshake, 0.0f, 1.0f);
                }
                shakePressureChanPressMod = (normmodshake * shakeModChanPressDepth);
            }
            if (IMUsettings[preset][Y_SHAKE_MOD_KEYPRESS]) {
                float normmodshake = basenormshake;
                if (IMUsettings[preset][Y_SHAKE_MOD_KEYPRESS_MODE] == Y_PITCHBEND_MODE_UPDOWN) {
                    normmodshake *= -1.0f;  // reverse phase
                } else if (IMUsettings[preset][Y_SHAKE_MOD_KEYPRESS_MODE] == Y_PITCHBEND_MODE_DOWNONLY) {
                    normmodshake = constrain(normmodshake, -1.0f, 0.0f);
                } else if (IMUsettings[preset][Y_SHAKE_MOD_KEYPRESS_MODE] == Y_PITCHBEND_MODE_UPONLY) {
                    normmodshake = constrain(-1.0f * normmodshake, 0.0f, 1.0f);
                } else if (IMUsettings[preset][Y_SHAKE_MOD_KEYPRESS_MODE] == Y_PITCHBEND_MODE_DOWNONLY_INV) {
                    normmodshake = constrain(1.0f * normmodshake, -1.0f, 0.0f);
                } else if (IMUsettings[preset][Y_SHAKE_MOD_KEYPRESS_MODE] == Y_PITCHBEND_MODE_UPONLY_INV) {
                    normmodshake = constrain(normmodshake, 0.0f, 1.0f);
                }
                shakePressureKeyPressMod = (int)(normmodshake * shakeModKeyPressDepth);
            }
        }
    }
}









// Return number of registers to jump based on IMU pitch (elevation).
int pitchRegister() {

    for (byte i = 1; i < IMUsettings[preset][PITCH_REGISTER_NUMBER] + 1; i++) {
        if (pitch < pitchRegisterBounds[i] || (i == IMUsettings[preset][PITCH_REGISTER_NUMBER] && pitch >= pitchRegisterBounds[i])) {  // See if IMU pitch is within the bounds for each register.
            return i - 1;
        }
    }

    return 0;
}









// Read incoming messages
void readMIDI(void) {

    MIDI.read();  // Read any new USBMIDI messages.

    if (Bluefruit.connected()) {        // Don't read if we aren't connected to BLE.
        if (blemidi.notifyEnabled()) {  // ...and ready to receive messages.
            BLEMIDI.read();             // Read new BLEMIDI messages.
        }
    }
}









// Monitor the status of the 3 buttons. The integrating debouncing algorithm is taken from debounce.c, written by Kenneth A. Kuhn:http://www.kennethkuhn.com/electronics/debounce.c
// NOTE: Button array is zero-indexed, so "button 1" in all documentation is button 0 here.
void checkButtons() {

    static byte integrator[] = { 0, 0, 0 };                // When this reaches MAXIMUM, a button press is registered. When it reaches 0, a release is registered.
    static bool prevOutput[] = { 0, 0, 0 };                // Previous state of button.
    bool buttonUsed = 0;                                   // Flag any button activity, so we know to handle it.
    static unsigned int longPressCounter[] = { 0, 0, 0 };  // For counting how many readings each button has been held, to indicate a long button press

    for (byte j = 0; j < 3; j++) {

        //20230629 MrMep - Timer for doubleclick
        if (waitingSecondClick[j] && doubleClickTimer++ > DOUBLE_CLICK_WAIT_INTERVAL) {  //We were waiting for a second click, but timer has exipired
            waitingSecondClick[j] = false;
        }

        if (digitalRead(buttons[j]) == 0) {  // If the button reads low, reduce the integrator by 1
            if (integrator[j] > 0) {
                integrator[j]--;
            }
        } else if (integrator[j] < MAXIMUM) {  // If the button reads high, increase the integrator by 1
            integrator[j]++;
        }


        if (integrator[j] == 0) {  // The button is pressed.
            pressed[j] = 1;        // We make the output the inverse of the input so that a pressed button reads as a "1".
            buttonUsed = 1;

            if (prevOutput[j] == 0 && !longPressUsed[j]) {
                justPressed[j] = 1;  // The button has just been pressed
            }

            else {
                justPressed[j] = 0;
            }

            if (prevOutput[j] == 1) {  // Increase a counter so we know when a button has been held for a long press.
                longPressCounter[j]++;
            }
        }


        else if (integrator[j] >= MAXIMUM) {  // The button is not pressed.
            pressed[j] = 0;
            integrator[j] = MAXIMUM;  // Defensive code if integrator got corrupted

            if (prevOutput[j] == 1 && !longPressUsed[j]) {
                released[j] = 1;                // The button has just been released.
                for (byte k = 0; k < 3; k++) {  //If any button has been released, reset all the long-press counters in case a button was being held only for the "hold 2 + click 1 or 3" gestures.
                    longPressCounter[k] = 0;    //
                }
                buttonUsed = 1;
            }

            longPress[j] = 0;
            longPressUsed[j] = 0;  // If a button is not pressed, reset the flag that tells us it's been used for a long press.
            longPressCounter[j] = 0;
        }


        if (longPressCounter[j] > 300 && !longPressUsed[j]) {  // If the counter gets to a certain level, it's a long press.
            longPress[j] = 1;
            longPressCounter[j] = 0;
            buttonUsed = 1;
        }

        prevOutput[j] = pressed[j];  // Keep track of state for next time around.
    }

    if (millis() < 1000) {  // Ignore button 3 for the first bit after powerup in case it was only being used to power on the device. ToDo?: Make it so the first release after startup isn't registered because if you hold 3 longer than 1 second it will still register.
        pressed[2] = 0;
        released[2] = 0;
    }

    if (buttonUsed) {
        handleButtons();  // If a button had been used, process the command. We only do this when we need to, so we're not wasting time.
    }

    buttonUsed = 0;  // Now that we've handled any important button activity, clear the flag until there's been new activity.
}









// Determine which holes are covered.
void getFingers() {

    for (byte i = 0; i < 9; i++) {
        const int caloffset = calibration > 0 ? (int)((toneholeCovered[i] - toneholeBaseline[i]) * 0.2f) : 0;  // only need to apply this offset during calibration itself
        if ((toneholeRead[i]) > (toneholeCovered[i] - toneholeBaseline[i] - caloffset)) {
            bitWrite(holeCovered, i, 1);  // Use the tonehole readings to decide which holes are covered
        } else if ((toneholeRead[i]) <= (toneholeCovered[i] - toneholeBaseline[i] - caloffset - 4)) {
            bitWrite(holeCovered, i, 0);  // Decide which holes are uncovered -- the "hole uncovered" reading is a little less then the "hole covered" reading, to prevent oscillations.
        }
    }

    if (breathMode == kPressureThumb && (bitRead(ED[preset][HALFHOLE_HOLES_HIGH4BITS], 3) == 1)) {  // If we're using the thumb for register shift, go ahead and detect the state now.
        getThumbHalfhole();
    }
}









// Thumb half hole handing for register control (called from getShift). For clarity this is separate from the function used for other fingers below.
void getThumbHalfhole() {

    int heightOffset = ED[preset][THUMB_HALFHOLE_HEIGHT_OFFSET];   // (0-100) Height offset below (0-50) or above (51-100)  the "natural" semitone point where the halfhole region is centered.
    int width = 50;                                                // It doesn't really make sense to use size for thumb, because there's never a "not halfhole" apace below the halfhole region. I'm just setting it to 50 for now. AM 4/26
    float fingerRate = ED[preset][THUMB_HALFHOLE_FINGERRATE] / 3;  // 0-127. Only used if not using slide too. The finger movement rate (in normalized sensor counts per reading) below which we'll snap to the semitone. Has the effect of a transient filter but uses finger rate rather than elapsed time so we only need to take two readings to calulate it.
    const int hysteresis = 3;                                      // Hysteresis for the target region
    bool inTargetRegion = halfHoleTargetRegionState[8];            // Whether the thumb is in the assigned halfhole region, initialized with last state
    static int prevToneholeRead;                                   // For calculating rate of finger movement
    float change = 999;                                            // Rate of finger movement
    static bool prevThumbHalfhole = 0;

    if (bitRead(holeCovered, 8) == 0) {                                                     // Only check the half hole state if it's not covered.
        change = (abs(sqrt(float(toneholeRead[8])) - sqrt(float(prevToneholeRead)))) * 30;  // Absolute rate of thumb movement, linearized to account for exponential sensor/distance relationship. Typically ranges from 0-100.
        prevToneholeRead = toneholeRead[8];

        int center = ((toneholeCovered[8] - senseDistance) >> 1) + senseDistance;  // Center sensor value for current slide hole (midpoint of sensor readings).
        // Note that sensor values increase exponentially with distance so the center sensor value is not the center of the distance from the tone hole.

        heightOffset = ((heightOffset - 50) * center) / 50;  // Convert offset to a positive or negative sensor value.
        width = (width * (center + heightOffset)) / 100;     // Convert width to a sensor value.

        // Determine if the thumb is in the target region.
        if (toneholeRead[8] > (center - heightOffset - width) && toneholeRead[8] > (senseDistance + hysteresis)) {  // The halfhole region extends all the way down to the fully-covered hole.
            inTargetRegion = true;

        } else if ((toneholeRead[8] < (center - heightOffset - width - hysteresis)) || toneholeRead[8] < senseDistance + hysteresis) {
            inTargetRegion = false;
        }

        halfHoleTargetRegionState[8] = inTargetRegion;
        if (((change < fingerRate) || (ED[preset][THUMB_HALFHOLE_FINGERRATE] == 127)) && inTargetRegion) {  // Snap to half hole if the thumb is moving slowly enough and it is within the defined region.
            snapped[8] = true;
        }

        if (!inTargetRegion) {
            snapped[8] = false;
            thumbHalfHole = false;  // Unshift the register.
            if (halfHoleShift[8] == true) {
                halfHoleShift[8] = false;
            }
        }

        if (snapped[8] == true) {
            thumbHalfHole = true;  // Shift the register.
        }
    } else {
        thumbHalfHole = false;  // Turn off half hole if the hole is covered.
    }

    if (prevThumbHalfhole != thumbHalfHole) {
        thumbHalfHoleChanged = true;
    } else thumbHalfHoleChanged = false;
    prevThumbHalfhole = thumbHalfHole;
}










// Detect changes in fingering. Contributions by Louis Barman and Jesse Chappell
void debounceFingerHoles() {

    static unsigned long debounceTimer;
    unsigned long now = millis();
    static bool timing;

    if (prevHoleCovered != holeCovered) {
        prevHoleCovered = holeCovered;
        debounceTimer = now;
        timing = 1;
        if (transientFilterDelay > 0 && isMaybeInTransition()) {
            transitionFilter = transientFilterDelay;  // ms timeout for transition to fail out
        } else {
            transitionFilter = 0;
        }
    }

    long debounceDelta = now - debounceTimer;

    if (transitionFilter > 0 && (debounceDelta >= transitionFilter || !isMaybeInTransition())) {  // Reset it if necessary.
#if DEBUG_TRANSITION_FILTER
        Serial.print(now);
        Serial.println(" canceltrans");
#endif
        transitionFilter = 0;
    }

    if ((debounceDelta >= transitionFilter
         && timing == 1)
        || thumbHalfHoleChanged == true) {  // The fingering pattern has changed. If we're using the thumb for register also check to see if the thumb has changed.
        thumbHalfHoleChanged = false;
        timing = 0;
        fingersChanged = 1;
        fingeringChangeTimer = millis();     // Start timing after the fingering pattern has changed.
        tempNewNote = getNote(holeCovered);  // Get the next MIDI note from the fingering pattern if it has changed. 3us.
        sendToConfig(true, false);           // Put the new pattern into a queue to be sent later so that it's not sent during the same connection interval as a new note (to decrease BLE payload size).

        if (tempNewNote != 127 && newNote != tempNewNote) {  // If a new note has been triggered (127 can be used as a "blank" position that has no effect),
            if (pitchBendMode != kPitchBendNone) {
                holeLatched = holeCovered;  // Remember the pattern that triggered it (it will be used later for vibrato).
                for (byte i = 0; i < 9; i++) {
                    iPitchBend[i] = 0;  // Reset pitchbend.
                    pitchBendOn[i] = 0;
                }
            }

#if DEBUG_TRANSITION_FILTER
            Serial.print(now);
            Serial.print(" : Commit: ");
            Serial.println(tempNewNote);
#endif

            newNote = tempNewNote;
            if (ED[preset][HALFHOLE_PITCHBEND] && ED[preset][HALFHOLE_USE_MIDI_NOTE]) {  // If we're halfholing to change the MIDI note, we need to calculate pitchbend again right before sending a note to avoid sending two notes rapidfire.
                calculateAndSendPitchbend();
            }
            getState();  // Get state again if the note has changed.
        }
    }
}









// This should be called right after a new hole state change, before sending out any new note.
bool isMaybeInTransition() {
    // Look at all finger hole states to see if there might be other
    // fingers in motion (partial hole covered) which means this
    // might be a multi-finger note transition and we may want to wait
    // a bit to see if the pending fingers land before triggering the new note.
    int pendingHoleCovered = holeCovered;
    unsigned long now = millis();

    for (byte i = 0; i < 9; i++) {
        int thresh = senseDistance;  //  ((toneholeCovered[i] - 50) - senseDistance) / 2;
        if (toneholeRead[i] > thresh) {
            if (bitRead(holeCovered, i) != 1) {
                bitWrite(pendingHoleCovered, i, 1);
            }
        }
    }

    if (pendingHoleCovered != holeCovered) {
        // See if the pending is a new note.
        byte tempNewNote = getNote(holeCovered);
        byte pendingNote = getNote(pendingHoleCovered);
        if (pendingNote != 127 && pendingNote != tempNewNote) {
#if DEBUG_TRANSITION_FILTER
            Serial.print(now);
            Serial.print(" : Maybe: ");
            Serial.print(pendingNote);
            Serial.print(" wait on: ");
            Serial.println(tempNewNote);
#endif
            return true;
        }
    }

    return false;
}











// Stream data to the standalone WARBL2 diagnostics page.
// A frame is sent ~every 50 ms. The frame order is fixed to avoid spending a
// selector CC on every individual sensor value.
void sendDiagnosticData(bool sendNow) {

    if (!diagnosticMode) {
        return;
    }

    sendMIDICouplet(MIDI_SEND_BATTERY_VOLTAGE, (((smoothed_voltage + 0.005f) * 100.0f) - 50.0f));

    // CC106/78 marks the beginning of a 26-byte CC119 frame:
    // hardware revision (1), runtime minutes (2), signed 32-bit pressure (5), nine toneholes (18).
    sendMIDI(MIDI_CC_106_MSG, MIDI_DIAGNOSTIC_FRAME);

    sendMIDI(MIDI_CC_119_MSG, diagnosticHardwareRevision);

    unsigned int runtime = constrain(diagnosticRunTimePerCharge, 0, 16383);
    sendMIDI(MIDI_CC_119_MSG, runtime & 0x7F);
    sendMIDI(MIDI_CC_119_MSG, (runtime >> 7) & 0x7F);

    // Preserve the complete signed int pressure value. MIDI data bytes are only 7 bits,
    // so transmit the raw 32-bit two's-complement representation in five chunks.
    uint32_t pressure = (uint32_t)((int32_t)twelveBitPressure);
    sendMIDI(MIDI_CC_119_MSG, (pressure >> 0) & 0x7F);
    sendMIDI(MIDI_CC_119_MSG, (pressure >> 7) & 0x7F);
    sendMIDI(MIDI_CC_119_MSG, (pressure >> 14) & 0x7F);
    sendMIDI(MIDI_CC_119_MSG, (pressure >> 21) & 0x7F);
    sendMIDI(MIDI_CC_119_MSG, (pressure >> 28) & 0x0F);

    // The firmware array is Bell=0 ... Thumb=8. Send it in reverse order so the web page
    // receives Thumb first and Bell last, matching the physical top-to-bottom display.
    for (int i = 8; i >= 0; i--) {
        unsigned int reading = constrain(toneholeRead[i], 0, 16383);
        sendMIDI(MIDI_CC_119_MSG, reading & 0x7F);
        sendMIDI(MIDI_CC_119_MSG, (reading >> 7) & 0x7F);
    }
}













// Send the finger pattern and pressure to the Configuration Tool after a delay to prevent sending during the same connection interval as a new MIDI note.
void sendToConfig(bool newPattern, bool newPressure) {

    static bool patternChanged = false;
    static bool pressureChanged = false;
    static unsigned long patternSendTimer;
    static unsigned long pressureSendTimer;

    unsigned long nowtime = millis();

    if (communicationMode) {
        if (newPattern && patternChanged == false) {  // If the fingering pattern has changed, start a timer.
            patternChanged = true;
            patternSendTimer = nowtime;
        }

        if (newPressure && pressureChanged == false) {  // If the pressure has changed, start a timer.
            pressureChanged = true;
            pressureSendTimer = nowtime;
        }

        if (patternChanged && (nowtime - patternSendTimer) > 25) {                              // If some time has past, send the new pattern to the Config Tool.
            sendMIDICouplet(MIDI_CC_114, holeCovered >> 7, MIDI_CC_115, lowByte(holeCovered));  // Because it's MIDI we have to send it in two 7-bit chunks.
            patternChanged = false;
        }

        int positiveSensorValue = sensorValue;
        if (positiveSensorValue < 0) {
            positiveSensorValue = 0;
        }

        if (pressureChanged && (nowtime - pressureSendTimer) > 25) {  // If some time has past, send the new pressure to the Config Tool.
            sendMIDICouplet(MIDI_CC_116, positiveSensorValue & 0x7F, MIDI_CC_118, positiveSensorValue >> 7);
            pressureChanged = false;
        }
    }
}











// Return a MIDI note number (0-127) based on the current fingering.
byte getNote(unsigned int fingerPattern) {
    byte ret = 127;  // Default (blank position)

    uint8_t tempCovered = fingerPattern >> 1;  // Bitshift once to ignore bell sensor reading.

    // Read the MIDI note for the current fingering (all charts except the custom ones).
    if (modeSelector[preset] < kWARBL2Custom1) {
        if (breathMode == kPressureThumb && (modeSelector[preset] == kModeEVI2 || modeSelector[preset] == kModeEVI3)) {  // Here we can put fingering charts that have the thumb hard-coded but we want to optionally be able to ignore the second half of the chart and use the thumb register and halfhole functionality instead.
            bitClear(tempCovered, 7);
        }
        ret = charts[modeSelector[preset]][tempCovered];

        if (modeSelector[preset] == kModeRecorder2 && thumbHalfHole == false) {  // Some special cases with Recorder2 if the thumb hole is completely open.
            if (tempCovered == 0b01100000) {
                ret = 73;
            } else if (tempCovered == 0b00100000) {
                ret = 74;
            } else if (tempCovered == 0b00111110) {
                ret = 75;
            }
        }

    } else {                                 // Otherwise read from the currently selected custom chart.
        if (breathMode == kPressureThumb) {  // If we're using the thumb for register control we only look at the first half of the custom chart (ignoring the half with the thumb hole covered).
            bitClear(tempCovered, 7);
        }
        ret = WARBL2CustomChart[tempCovered];
    }

    // For whistle and uilleann also read the vibrato flag for the current fingering.
    if (modeSelector[preset] == kModeWhistle || modeSelector[preset] == kModeChromatic) {
        vibratoEnable = whistleVibrato[tempCovered];
    }

    if (modeSelector[preset] == kModeUilleann || modeSelector[preset] == kModeUilleannStandard) {
        vibratoEnable = uilleannVibrato[tempCovered];
    }

    if ((modeSelector[preset] == kModeNorthumbrian && ret == 63) || (breathMode != kPressureBell && holeCovered == 0b111111111))  // Play silence if all holes incuding bell sensor are covered, or if we're in Northumbrian mode and all top sense and thumb are covered. That simulates the closed pipe.
    {
        ret = 0;  // Silence
    }


    return ret;
}









// Add up any transposition based on key and register.
void getShift() {
    shift = getShiftInternal(newState, holeCovered, newNote);
}

int8_t getShiftInternal(int l_newState, int l_holeCovered, int l_newNote) {


    byte pitchShift;
    byte totalHalfHoleShift = 0;

    for (byte i = 0; i < 9; i++) {
        if (halfHoleShift[i] == true) {  // See if any hole contributes to halfHole MIDI note shift.
            totalHalfHoleShift = -1;
        }
    }

    if (IMUsettings[preset][PITCH_REGISTER] == true) {
        pitchShift = pitchRegister();
    }

    int8_t lshift = ((octaveShift * 12) + noteShift + (pitchShift * ED[preset][OVERBLOW_SEMITONES]) + totalHalfHoleShift);  // Adjust for key and octave shift.

    // Overblow if allowed.
    if (l_newState == TOP_REGISTER && !(modeSelector[preset] == kModeEVI || (modeSelector[preset] == kModeSax && l_newNote < 58) || (modeSelector[preset] == kModeSaxBasic && l_newNote < 70) || (modeSelector[preset] == kModeRecorder && l_newNote < 74)) && !(l_newNote == 62 && (modeSelector[preset] == kModeUilleann || modeSelector[preset] == kModeUilleannStandard))) {  // If overblowing (except EVI, sax and recorder in the lower register, and low D with uilleann fingering, which can't overblow)
        lshift = lshift + ED[preset][OVERBLOW_SEMITONES];                                                                                                                                                                                                                                                                                                                         // Add a register jump to the transposition if overblowing.
        if (modeSelector[preset] == kModeKaval) {                                                                                                                                                                                                                                                                                                                                 // Kaval only plays a fifth higher in the second register.
            lshift = lshift - 5;
        }
    }
    // Use the bell sensor to control register if desired.
    if (breathMode == kPressureBell && modeSelector[preset] != kModeUilleann && modeSelector[preset] != kModeUilleannStandard) {
        if (bitRead(l_holeCovered, 0) == switches[preset][INVERT]) {
            lshift = lshift + ED[preset][OVERBLOW_SEMITONES];
            if (modeSelector[preset] == kModeKaval) {
                lshift = lshift - 5;
            }
        }
    }

    // ToDo: Are there any others that don't use the thumb that can be added here?
    // If we're using the left thumb to control the regiser with a fingering patern that doesn't normally use the thumb
    else if ((breathMode == kPressureThumb && (modeSelector[preset] == kModeEVI2 || modeSelector[preset] == kModeEVI3 || modeSelector[preset] == kWARBL2Custom1 || modeSelector[preset] == kWARBL2Custom2 || modeSelector[preset] == kWARBL2Custom3 || modeSelector[preset] == kWARBL2Custom4 || modeSelector[preset] == kModeWhistle || modeSelector[preset] == kModeChromatic || modeSelector[preset] == kModeNAF))) {
        byte thumbShift = getThumbHalfHoleShift(l_holeCovered);           // Number of registers shifted by thumb
        lshift = lshift + (thumbShift * ED[preset][OVERBLOW_SEMITONES]);  // Add an octave jump to the transposition if necessary.
    }

    return lshift;
}









// Get the number of registers shifted by the thumb.
byte getThumbHalfHoleShift(int l_holeCovered) {

    /* Thumb halfhole function (table from MrMep)
_________________________________________________________________________________________________
|   Invert Thumb/Bell |   Invert Half Thumb |  1st octave |   2nd octave  |   3rd octave  |
_________________________________________________________________________________________________
|         off         |         off          |     closed  |      half     |      open     |
|         on          |         off          |      open   |      half     |     closed    |
|         off         |         on           |     closed  |      open     |      half     |
|         on          |         on           |      open   |     closed    |      half     |
_________________________________________________________________________________________________

*/
    const byte lookup[4][3] = { { 1, 3, 2 }, { 1, 2, 3 }, { 3, 1, 2 }, { 2, 1, 3 } };           // Lookup table for thumb halfhole functionality.
    byte combinedSwitches = switches[preset][INVERT] << 1 | ED[preset][HALFHOLE_INVERT_THUMB];  // Append the invert switches for the first dimension of the lookup table.
    byte thumbPosition = thumbHalfHole ? 2 : 1 - bitRead(l_holeCovered, 8);                     // Second dimension is thumb position: 0 closed, 1 open, 2 half


    if (modeSelector[preset] != kModeRecorder2) {                                                     // Recorder2 is handled in getNote(), so ignore that.
        if (!(ED[preset][HALFHOLE_PITCHBEND] && bitRead(ED[preset][HALFHOLE_HOLES_HIGH4BITS], 3))) {  // First handle register contribution by the thumb if we're not using it for half-holing.
            if (bitRead(l_holeCovered, 8) == switches[preset][INVERT]) {
                return 1;
            } else {
                return 0;
            }
        }

        else {  // If thumb halfhole is being used
            return lookup[combinedSwitches][thumbPosition] - 1;
        }
    } else {
        return 0;  // There's no thumb shift with Recorder2-- we just need to get the thumb state.
    }
}









// This mode is currently "hidden" -- to turn it on select "-18" in the transpose menu and then click "Learn" in the drones control panel within 10 seconds.
// Use IMU elevation angle to prevent overblowing from changing the current register (allow finer control of dynamics within the current register).
void getRegisterHold() {

    if (ED[preset][ENABLE_REGISTER_HOLD]) {

        // Settings
        const byte registerHoldMode = 4;      // 1 = hold both registers (both tilt zones), 2 = hold low register only (both tilt zones), 3 = hold high register only (both tilt zones), 4 = hold low register with low tilt zone and high register with high tilt zone.
        const float lowerHoldAngle = -75.0f;  // Elevation angle below which the register will be locked (can be set at -90 for no lower lock zone).
        const float upperHoldAngle = -20.0f;  // Elevation angle above which the register will be locked (can be set at 90 for no upper lock zone).

        bool inTiltZone = false;

        if ((registerHoldMode == 1 || (registerHoldMode < 4 && registerHoldMode == newState)) && (pitch < lowerHoldAngle || pitch > upperHoldAngle)) {  // Modes 1-3
            inTiltZone = true;
        }

        if (registerHoldMode == 4 && ((pitch < lowerHoldAngle && newState == 2) || (pitch > upperHoldAngle && newState == 3))) {  // Mode 4
            inTiltZone = true;
        }

        if (inTiltZone) {
            if (!registerHold && newState != SILENCE) {
                registerHold = true;
                heldRegister = newState;
            }
        } else if ((registerHoldMode < 4 && pitch >= lowerHoldAngle && pitch <= upperHoldAngle) || (registerHoldMode == 4 && ((pitch >= lowerHoldAngle && heldRegister == 2) || (pitch <= upperHoldAngle && heldRegister == 3)))) {  // Reset if we've exited the hold zones.
            registerHold = false;
        }
    }
}








// State machine that models the way that a tinwhistle etc. begins sounding and jumps octaves in response to breath pressure.
// The current jump/drop behavior is from Louis Barman
void getState() {

    byte scalePosition;  // ScalePosition is used to tell where we are on the scale, because higher notes are more difficult to overblow.
    unsigned int tempHoleCovered = holeCovered;
    bitSet(tempHoleCovered, 8);                                  // Ignore thumb hole.
    scalePosition = findleftmostunsetbit(tempHoleCovered) + 62;  // Use the highest open hole to calculate. ToDo: This could be rewritten because soe charts may ignore upper holes. Maybe use the number of uncovered holes or something like that?
    if (scalePosition > 69) {
        scalePosition = 70;
    }

    if (ED[preset][DRONES_CONTROL_MODE] == 3) {  // Use pressure to control drones if that option has been selected. There's a small amount of hysteresis added.

        if (!dronesOn && sensorValue > 5 + (ED[preset][DRONES_PRESSURE_HIGH_BYTE] << 7 | ED[preset][DRONES_PRESSURE_LOW_BYTE])) {
            startDrones();
        }

        else if (dronesOn && sensorValue < (ED[preset][DRONES_PRESSURE_HIGH_BYTE] << 7 | ED[preset][DRONES_PRESSURE_LOW_BYTE])) {
            stopDrones();
        }
    }

    upperBound = (sensorThreshold[1] + ((scalePosition - 60) * multiplier));  // Calculate the threshold between state 2 (bottom register) and state 3 (top register). This will also be used to calculate expression.

    newState = currentState;

    if (sensorValue <= sensorThreshold[0]) {
        newState = SILENCE;
        holdoffActive = false;                                                                 // No need to wait for jump/drop if we've already crossed the threshold for silence
    } else if (sensorValue > (sensorThreshold[0] + ED[preset][SILENCE_HYSTERESIS] * 2) - 1) {  // Allow a minumum valule of 1 for hysteresis.
        if (currentState == SILENCE) {
            newState = BOTTOM_REGISTER;
        }


        if (breathMode == kPressureBreath) {  // If overblowing is enabled
            upperBoundHigh = calcHysteresis(upperBound, true);
            upperBoundLow = calcHysteresis(upperBound, false);
            if (sensorValue > upperBoundHigh) {
                newState = TOP_REGISTER;
                holdoffActive = false;
            } else if (sensorValue <= upperBoundLow) {
                newState = BOTTOM_REGISTER;
            }

            // Wait to decide about jump or drop if necessary.
            if (currentState == SILENCE && newState == BOTTOM_REGISTER) {
                newState = delayStateChange(JUMP, sensorValue, upperBoundHigh);
            } else if (currentState == TOP_REGISTER && newState == BOTTOM_REGISTER && (millis() - fingeringChangeTimer) > 20) {  // Only delay for drop if the note has been playing for a bit. This fixes erroneous high-register notes.
                newState = delayStateChange(DROP, sensorValue, upperBoundLow);
            }
        }
    }

    if (registerHold && newState != SILENCE) {  // If register is locked, only allow silence or the held register.
        newState = heldRegister;
    }

    currentState = newState;

    if (switches[preset][SEND_VELOCITY]) {  // If we're sending NoteOn velocity based on pressure,
        if (prevState == SILENCE && newState != SILENCE) {
            velocityDelayTimer = millis();  // reset the delay timer used for calculating velocity when a note is turned on after silence.
        }
        prevState = newState;
    }
}







// Delay the overblow state until either it has timed out or the pressure has leveled off.
byte delayStateChange(byte jumpDrop, int pressure, int upper) {
    static unsigned long holdOffTimer;
    unsigned long now = millis();
    bool exitEarly = false;
    int rateChange;

    if (!holdoffActive) {  // Start our timer if we haven't already.
        holdoffActive = true;
        holdOffTimer = now;
        rateChangeIdx = 0;
        previousPressure = 0;
    }

    if ((jumpDrop == JUMP && (now - holdOffTimer) < jumpTime) || (jumpDrop == DROP && (now - holdOffTimer) < dropTime)) {  // If we haven't paused long enough, check the pressure rate change to see if it has leveled off.


        rateChange = pressureRateChange(pressure);

        if (rateChange != 2000) {  // Make sure it's valid
            if (jumpDrop == JUMP && rateChange <= 0) {
                exitEarly = true;
            } else if (jumpDrop == DROP && rateChange >= 0) {
                exitEarly = true;
            }
        }
    }

    // If we've paused long enough or the pressure has stabilized, go to the bottom register
    else {
        holdoffActive = false;
        return BOTTOM_REGISTER;
    }

    if (exitEarly) {
        holdoffActive = false;
        return BOTTOM_REGISTER;
    }

    return currentState;  // Stay in the current state if we haven't waited the total time and the pressure hasn't yet leveled off.
}








// Calculate the rate of pressure change to see if the slope has reversed
int pressureRateChange(int pressure) {
    int rateChange = 2000;  // If not valid
    if (rateChangeIdx == 0) {
        rateChangeIdx = 1;
        previousPressure = pressure;
    } else {
        rateChange = pressure - previousPressure;
        previousPressure = pressure;
    }

    return rateChange;
}








// Calculate the upper boundary for the register when hysteresis is applied, from Louis Barman.
int calcHysteresis(int currentUpperBound, bool high) {
    if (hysteresis == 0) {
        return currentUpperBound;
    }
    int range = currentUpperBound - sensorThreshold[0];
    int newUpperBound;
    if (high) {
        newUpperBound = currentUpperBound + (range * hysteresis) / 400;
    } else {
        newUpperBound = currentUpperBound - (range * hysteresis * 3) / 400;
    }

    return newUpperBound;
}









inline float curveValToExponent(int val) {
    // takes 0 -> 127 and returns curve exponent
    // which is between 0.25 -> 1.0 -> 4.0
    float retval = 1.0f;
    val -= 64;
    if (val >= 0) {
        retval = ((3.0f * val / 63.0f) + 1.0f);
    } else {
        retval = (0.75f * (64.0f + val) / 64.0f + 0.25f);
    }
    return retval;
}








// Calculate the bend in a low and high pressure range segments, with a stable (no-bend) range between.
void getExpression() {

    int lowPressureMin = (ED[preset][EXPRESSION_MIN] * 9) + 100;
    int lowPressureMax = (ED[preset][EXPRESSION_MIN_HIGH] * 9) + 100;
    int highPressureMin = (ED[preset][EXPRESSION_MAX_LOW] * 9) + 100;
    int highPressureMax = (ED[preset][EXPRESSION_MAX] * 9) + 100;
    int centsLowOffset = 2 * (ED[preset][EXPRESSION_OUT_LOW_CENTS] - 64);
    int centsHighOffset = 2 * (ED[preset][EXPRESSION_OUT_HIGH_CENTS] - 64);
    float lowCurveExp = curveValToExponent(ED[preset][EXPRESSION_CURVE_LOW]);
    float highCurveExp = curveValToExponent(ED[preset][EXPRESSION_CURVE_HIGH]);
    bool doClamp = ED[preset][EXPRESSION_OUT_CLAMP] > 0;

    // Fixed non-override options or overblow mode
    if (!switches[preset][OVERRIDE] || (breathMode == kPressureBreath)) {
        if (newState == TOP_REGISTER) {
            lowPressureMin = upperBoundLow;                                                  // sensorThreshold[0];  // Otherwise use boundaries based on the pressure range of the current register.
            highPressureMax = upperBoundLow + ((upperBoundHigh - sensorThreshold[0]) >> 1);  // Get the register boundary taking hysteresis into consideration.
        } else {
            lowPressureMin = sensorThreshold[0];  // Otherwise use boundaries based on the pressure range of the current register.
            if (breathMode == kPressureBreath) {
                highPressureMax = upperBoundHigh;
            } else {
                int centerPressure = (ED[preset][EXPRESSION_FIXED_CENTER_PRESSURE] * 9) + 100;
                highPressureMax = 2 * (centerPressure - lowPressureMin) + lowPressureMin;
            }
        }

        // Make them meet in the middle.
        lowPressureMax = highPressureMin = ((highPressureMax + lowPressureMin) >> 1);

        // May need to play with these - XXX
        centsLowOffset = -20 * ED[preset][EXPRESSION_DEPTH];  // -20 cents at least
        centsHighOffset = ((breathMode == kPressureBreath) ? 10 : 20) * ED[preset][EXPRESSION_DEPTH];
        doClamp = true;
        lowCurveExp = 1.0f;
        highCurveExp = 1.0f;
    }

    float centsOffset = 0.0f;
    float ratio = 0.0f;
    int lowRangeSpan = max(lowPressureMax - lowPressureMin, 1);
    int highRangeSpan = max(highPressureMax - highPressureMin, 1);
    if (sensorValue <= lowPressureMax) {  // Pressure is in the lower range.
        ratio = min(((lowPressureMax - sensorValue)) / (float)(lowRangeSpan), 1.0f);
        if (lowCurveExp != 1.0f) {
            ratio = powf(ratio, lowCurveExp);
        }
        centsOffset = centsLowOffset * ratio;
    } else if (sensorValue >= highPressureMin) {  // Pressure is in the higher range.
        ratio = max(((sensorValue - highPressureMin)) / (float)(highRangeSpan), 0.0f);
        if (highCurveExp != 1.0f) {
            ratio = powf(ratio, highCurveExp);
        }
        if (doClamp) {
            ratio = min(ratio, 1.0f);
        }
        centsOffset = centsHighOffset * ratio;
    } else {
        // In the stable range
        centsOffset = 0;
    }

    expression = (int)(0.01f * centsOffset * pitchBendPerSemi);  // Expression is in raw pitch bend units.
}








// Calculate the bend in a low and high IMU range segments, with a stable (no-bend) range between.
void getIMUpitchbend() {

    IMUpitchbend = 0;  // Reset.

    for (byte i = 0; i < 3; i++) {
        if (IMUsettings[preset][MAP_ROLL_TO_PITCHBEND + i]) {  // Calculate pitchbend separately for roll, pitch, and yaw if necessary.
            int IMUvalue;
            if (i == 0) {
                IMUvalue = ((constrain(roll, -90, 90) + 90) * 5) + 100;  // Constrain roll to 180 degrees and map to same range as pressure sensor, for re-using expression calculations.
            }
            if (i == 1) {
                IMUvalue = ((constrain(pitch, -90, 90) + 90) * 5) + 100;  // Pitch
            }
            if (i == 2) {                                                             // Changed by AM 3/26 to use compass direction (axisHeading) rather than yaw.
                IMUvalue = ((constrain(axisHeading, -180, 180) + 180) * 2.5f) + 100;  // Yaw (full 360 degree range)
            }
            int lowIMUmin = (IMUsettings[preset][IMU_ROLL_PITCH_MIN + (i * 9)] * 25) + 100;  // Values received from the Config Tool range from 0-36 and we scale them up to 900 here to make it easy to re-use the calculations from the expression override function above.
            int lowIMUmax = (IMUsettings[preset][IMU_ROLL_PITCH_MIN_HIGH + (i * 9)] * 25) + 100;
            int highIMUmin = (IMUsettings[preset][IMU_ROLL_PITCH_MAX_LOW + (i * 9)] * 25) + 100;
            int highIMUmax = (IMUsettings[preset][IMU_ROLL_PITCH_MAX + (i * 9)] * 25) + 100;
            int centsLowOffset = 2 * (IMUsettings[preset][IMU_ROLL_PITCH_OUT_LOW_CENTS + (i * 9)] - 64);
            int centsHighOffset = 2 * (IMUsettings[preset][IMU_ROLL_PITCH_OUT_HIGH_CENTS + (i * 9)] - 64);
            float lowCurveExp = curveValToExponent(IMUsettings[preset][IMU_ROLL_PITCH_CURVE_LOW + (i * 9)]);
            float highCurveExp = curveValToExponent(IMUsettings[preset][IMU_ROLL_PITCH_CURVE_HIGH + (i * 9)]);
            bool doClamp = IMUsettings[preset][IMU_ROLL_PITCH_OUT_CLAMP + (i * 9)] > 0;
            float centsOffset = 0.0f;
            float ratio = 0.0f;
            int lowRangeSpan = max(lowIMUmax - lowIMUmin, 1);
            int highRangeSpan = max(highIMUmax - highIMUmin, 1);
            if (IMUvalue <= lowIMUmax) {  // IMU is in the lower range.
                ratio = ((lowIMUmax - IMUvalue)) / (float)(lowRangeSpan);
                if (lowCurveExp != 1.0f) {
                    ratio = powf(ratio, lowCurveExp);
                }
                if (doClamp) {
                    ratio = min(ratio, 1.0f);
                }
                centsOffset = centsLowOffset * ratio;
            } else if (IMUvalue >= highIMUmin) {  // IMU is in the higher range.
                ratio = max(((IMUvalue - highIMUmin)) / (float)(highRangeSpan), 0.0f);
                if (highCurveExp != 1.0f) {
                    ratio = powf(ratio, highCurveExp);
                }
                if (doClamp) {
                    ratio = min(ratio, 1.0f);
                }
                centsOffset = centsHighOffset * ratio;
            } else {
                // In the stable range
                centsOffset = 0;
            }

            IMUpitchbend += (int)(0.01f * centsOffset * pitchBendPerSemi);  // Add in contribution by roll, pitch, yaw. In raw pitch bend units.
        }
    }
}









// For a specific hole, return the number of half-step intervals it would be from the current note with hole-covered state.
int findStepsOffsetFor(int hole) {
    unsigned int closedHolePattern = holeCovered;
    bitSet(closedHolePattern, hole);  // Figure out what the fingering pattern would be if we closed the hole.
    int oldNote = getNote(closedHolePattern);
    int stepsOffset = oldNote - newNote;

    int oldShift = getShiftInternal(newState, closedHolePattern, oldNote);
    stepsOffset += oldShift - shift;

    return stepsOffset;
}










// Custom pitchbend algorithms, tin whistle and uilleann by Michael Eskin
void handleCustomPitchBend() {
    for (byte i = 0; i < 9; i++) {  // Reset all holes
        iPitchBend[i] = 0;
    }

    if (pitchBendMode == kPitchBendSlideVibrato || pitchBendMode == kPitchBendLegatoSlideVibrato || ED[preset][HALFHOLE_PITCHBEND]) {  // Calculate slide and halfhole if necessary.
        getSlide();
    }

    if (pitchBendMode != kPitchBendNone) {  // If halfhole pitchbend is enabled but no other pitchbend is, we don't need to calculate any vibrato.

        // This method only cares if 2 or 3 are slideholes.
        int slideHoleIndex = iPitchBend[2] != 0 ? 2 : iPitchBend[3] != 0 ? 3
                                                                         : 0;

        if (modeSelector[preset] != kModeGHB && modeSelector[preset] != kModeNorthumbrian) {  // Only used for whistle and uilleann
            if (vibratoEnable == 1) {                                                         // If it's a vibrato fingering pattern
                if (iPitchBend[2] == 0) {
                    iPitchBend[2] = adjvibdepth;  // Just assign max vibrato depth to a hole that isn't being used for sliding (it doesn't matter which hole, it's just so it will be added in later).
                    iPitchBend[3] = 0;
                } else if (iPitchBend[3] == 0) {
                    iPitchBend[3] = adjvibdepth;
                    iPitchBend[2] = 0;
                }
            }


            if (vibratoEnable == 2) {  // Used for whistle and uilleann, indicates that it's a pattern where lowering finger 2 or 3 partway would trigger progressive vibrato.

                if (modeSelector[preset] == kModeWhistle || modeSelector[preset] == kModeChromatic) {
                    for (byte i = 2; i < 4; i++) {
                        if ((toneholeRead[i] > senseDistance) && (bitRead(holeCovered, i) != 1 && (i != slideHoleIndex))) {  // If the hole is contributing, bend down.
                            iPitchBend[i] = (int)((toneholeRead[i] - senseDistance) * vibratoScale[i]);
                        } else if (i != slideHoleIndex) {
                            iPitchBend[i] = 0;
                        }
                    }
                    if (slideHoleIndex != 2 && slideHoleIndex != 3 && iPitchBend[2] + iPitchBend[3] > adjvibdepth) {
                        iPitchBend[2] = adjvibdepth;  // Cap at max vibrato depth if they combine to add up to more than that (just set one to max and the other to zero).
                        iPitchBend[3] = 0;
                    }
                }

                else if (modeSelector[preset] == kModeUilleann || modeSelector[preset] == kModeUilleannStandard) {

                    if ((holeCovered & 0b100000000) == 0) {  // If the back-D is open, and the vibrato hole completely open, max the pitch bend.
                        if (bitRead(holeCovered, 3) == 1) {
                            iPitchBend[3] = 0;
                        } else {  // Otherwise, bend down proportional to distance
                            if (toneholeRead[3] > senseDistance) {
                                iPitchBend[3] = adjvibdepth - (((toneholeRead[3] - senseDistance) * vibratoScale[3]));
                            } else {
                                iPitchBend[3] = adjvibdepth;
                            }
                        }
                    } else {

                        if ((toneholeRead[3] > senseDistance) && (bitRead(holeCovered, 3) != 1) && 3 != slideHoleIndex) {
                            iPitchBend[3] = (int)((toneholeRead[3] - senseDistance) * vibratoScale[3]);
                        }

                        else if ((toneholeRead[3] < senseDistance) || (bitRead(holeCovered, 3) == 1)) {
                            iPitchBend[3] = 0;  // If the finger is removed or the hole is fully covered, there's no pitchbend contributed by that hole.
                        }
                    }
                }
            }
        }


        else if (modeSelector[preset] == kModeGHB || modeSelector[preset] == kModeNorthumbrian) {  // This one is designed for closed fingering patterns, so raising a finger sharpens the note.
            for (byte i = 2; i < 4; i++) {                                                         // Use holes 2 and 3 for vibrato.
                if (i != slideHoleIndex || (holeCovered & 0b100000000) == 0) {
                    static unsigned int testNote;                        // The hypothetical note that would be played if a finger were lowered all the way.
                    if (bitRead(holeCovered, i) != 1) {                  // If the hole is not fully covered
                        if (fingersChanged) {                            // If the fingering pattern has changed
                            testNote = getNote(bitSet(holeCovered, i));  // Check to see what the new note would be.
                            fingersChanged = 0;
                        }
                        if (testNote == newNote) {  // If the hole is uncovered and covering the hole wouldn't change the current note (or the left thumb hole is uncovered, because that case isn't included in the fingering chart).
                            if (toneholeRead[i] > senseDistance) {
                                iPitchBend[i] = 0 - (int)((max(toneholeCovered[i] - toneholeBaseline[i] - toneholeRead[i], 0) * vibratoScale[i]));  // Bend up, yielding a negative pitchbend value.
                            } else {
                                iPitchBend[i] = 0 - adjvibdepth;  // If the hole is totally uncovered, max the pitchbend.
                            }
                        }
                    } else {                // If the hole is covered
                        iPitchBend[i] = 0;  // Reset the pitchbend to 0
                    }
                }
            }
            if ((((iPitchBend[2] + iPitchBend[3]) * -1) > adjvibdepth) && ((slideHoleIndex != 2 && slideHoleIndex != 3) || (holeCovered & 0b100000000) == 0)) {  // Cap at vibrato depth if more than one hole is contributing and they add to up to more than the vibrato depth.
                iPitchBend[2] = 0 - adjvibdepth;                                                                                                                 // Assign max vibrato depth to a hole that isn't being used for sliding.
                iPitchBend[3] = 0;
            }
        }
    }
}









// Andrew's version of vibrato
void handlePitchBend() {
    for (byte i = 0; i < 9; i++) {  // Reset
        iPitchBend[i] = 0;
    }

    if (pitchBendMode == kPitchBendSlideVibrato || pitchBendMode == kPitchBendLegatoSlideVibrato || ED[preset][HALFHOLE_PITCHBEND]) {  // Calculate slide and halfhole if necessary.
        getSlide();
    }

    if (pitchBendMode != kPitchBendNone) {  // If halfhole pitchbend is enabled but no other pitchbend is, we don't need to calculate any vibrato.

        for (byte i = 0; i < 9; i++) {

            if (bitRead(holeLatched, i) == 1 && toneholeRead[i] < senseDistance) {
                (bitWrite(holeLatched, i, 0));  // We "unlatch" (enable for vibrato) a hole if it was covered when the note was triggered but now the finger has been completely removed.
            }

            if (bitRead(vibratoHoles, i) == 1 && bitRead(holeLatched, i) == 0  // If this is a vibrato hole and we're in a mode that uses vibrato, and the hole is unlatched
                && (iPitchBend[i] == 0)) {                                     // ...and not already being used for slide or halfhole
                if (toneholeRead[i] > senseDistance) {
                    if (bitRead(holeCovered, i) != 1) {
                        iPitchBend[i] = (int)(((toneholeRead[i] - senseDistance) * vibratoScale[i]));  //bend downward
                        pitchBendOn[i] = 1;
                    }
                } else {
                    pitchBendOn[i] = 0;
                    if (bitRead(holeCovered, i) == 1) {
                        iPitchBend[i] = 0;
                    }
                }

                if (bitRead(holeCovered, i) == 1) {
                    iPitchBend[i] = adjvibdepth;  // Set vibrato to max downward bend if a hole was being used to bend down and now is covered
                }
            }
        }
    }
}









void getSlide() {

    byte halfHoleEnabled = (ED[preset][HALFHOLE_HOLES_HIGH4BITS] << 4) | ED[preset][HALFHOLE_HOLES_LOW4BITS];

    int legatoSlideLimit = constrain(ED[preset][SLIDE_LIMIT_MAX], 0, midiBendRange);

    // Legacy slide/vibrato behavior.
    if (pitchBendModeSelector[preset] == kPitchBendSlideVibrato) {
        legatoSlideLimit = 2;
    }

    for (byte i = 0; i < 9; i++) {

        if ((bitRead(holeCovered, i) == 1) && i == previousTonehole) {  // For half hole: If a hole is covered, make sure two new sensor readings will be obtained for calculating finger rate.
            previousTonehole = 255;
        }

        if (toneholeRead[i] > senseDistance && bitRead(holeCovered, i) != 1 && transitionFilter == 0) {  // Does transitionFilter really need to be zero here? AM

            int offsetSteps = findStepsOffsetFor(i);
            int trueOffsetSteps = offsetSteps;

            if (pitchBendModeSelector[preset] == kPitchBendSlideVibrato && offsetSteps < -legatoSlideLimit) {  // Added by AM 5/24 to make the slide behavior more like that of the original WARBL.
                offsetSteps = -legatoSlideLimit;
            }

            if (!(ED[preset][HALFHOLE_PITCHBEND] && ED[preset][HALFHOLE_USE_MIDI_NOTE]) && !(ED[preset][HALFHOLE_PITCHBEND] && trueOffsetSteps == -2 && (i > 0 && bitRead(halfHoleEnabled, i - 1) == 1))) {  // Calculate slide normally if halfhole doesn't apply (if we're using half-holing and sending MIDI notes instead of pitch, we also don't use sliding on any holes).
                if ((pitchBendModeSelector[preset] == kPitchBendSlideVibrato || pitchBendModeSelector[preset] == kPitchBendLegatoSlideVibrato) && !(!ED[preset][USE_THUMB_FOR_SLIDE] && i == 8)) {

                    if (offsetSteps != 0 && offsetSteps <= legatoSlideLimit && offsetSteps >= -legatoSlideLimit) {
                        iPitchBend[i] = ((((int)((toneholeRead[i] - senseDistance) * toneholeScale[i])) * -offsetSteps));  // Scale.

                    } else {
                        iPitchBend[i] = 0;
                        snapped[i] = false;
                        halfHoleShift[i] = false;
                        halfHoleTargetRegionState[i] = false;
                    }
                }
            } else if (i != 8 && trueOffsetSteps == -2 && (i > 0 && bitRead(halfHoleEnabled, i - 1) == 1)) {  // Calculate halfhole pitchbend if all the conditions for this hole are met.
                getHalfholePitchbend(i);
            }

        } else {
            iPitchBend[i] = 0;
            snapped[i] = false;
            halfHoleShift[i] = false;
            halfHoleTargetRegionState[i] = false;
        }
    }
}









// Snap pitchbend to a semitone (or optionally apply a shift to the MIDI note) and optionally calculate slide to smoothly integrate.
void getHalfholePitchbend(byte i) {

    int heightOffset = ED[preset][HALFHOLE_HEIGHT_OFFSET];   // (0-100) Height offset below (0-50) or above (51-100)  the "natural" semitone point where the halfhole region is centered.
    int width = ED[preset][HALFHOLE_WIDTH];                  // The size of the halfhole region (%). Lower values require more accurate finger placement but leave more room for sliding (and smoother transitions from sliding to semitone).
    int fingerRate = ED[preset][HALFHOLE_FINGERRATE] * 1.5;  // 0-127. Only used if not using slide too. The finger movement rate (in normalized sensor counts per reading) below which we'll snap to the semitone. Has the effect of a transient filter but uses finger rate rather than elapsed time so we only need to take two readings to calulate it.
    const int hysteresis = 3;                                // Hysteresis for the target region
    bool inTargetRegion = halfHoleTargetRegionState[i];      // Whether the finger is in the assigned halfhole region, initialized with last state
    const int offsetSteps = -2;                              // This is always true because there is a full step drop for the holes we use for halfholing.
    static int prevToneholeRead[9];                          // For calculating rate of finger movement
    bool inSlideHyst = false;
    float change = 999;  // Rate of finger movement


    if (i == previousTonehole) {
        change = (abs(sqrt(float(toneholeRead[i])) - sqrt(float(prevToneholeRead[i])))) * 30;  // Absolute rate of finger movement, linearized to account for exponential sensor/distance relationship. Typically ranges from 0-100.
        prevToneholeRead[i] = toneholeRead[i];
    }

    previousTonehole = i;

    int center = ((toneholeCovered[i] - senseDistance) >> 1) + senseDistance;  // Center sensor value for current slide hole (midpoint of sensor readings).
    // Note that sensor values increase exponentially with distance so the center sensor value is not the center of the distance from the tone hole.

    heightOffset = ((heightOffset - 50) * center) / 50;  // Convert offset to a positive or negative sensor value.
    width = (width * (center + heightOffset)) / 100;     // Convert width to a sensor value.

    // Determine if the finger is in the target region.
    if ((pitchBendModeSelector[preset] == kPitchBendSlideVibrato || pitchBendModeSelector[preset] == kPitchBendLegatoSlideVibrato) && !ED[preset][HALFHOLE_USE_MIDI_NOTE]) {
        if (abs(toneholeRead[i] - center + heightOffset) < width && toneholeRead[i] > (senseDistance + hysteresis)) {  // If we're using slide, there's a "not halfhole" space both above and below the halfhole region.
            inTargetRegion = true;

        } else if (abs(toneholeRead[i] - center + heightOffset) > width + hysteresis && toneholeRead[i] > (senseDistance + hysteresis)) {  // Use hysteresis to exit target region to avoid oscillations when we're not also using slide.
            inTargetRegion = false;

        } else {
            inSlideHyst = toneholeRead[i] <= (senseDistance + hysteresis);
        }
    } else if (toneholeRead[i] > (center - heightOffset - width) && toneholeRead[i] > (senseDistance + hysteresis)) {  // If we're not using sliding, if we're using MIDI notes for pitchbend, or using the thumb for register, the halfhole region extends all the way down to the fully-covered hole.
        inTargetRegion = true;

    } else if ((toneholeRead[i] < (center - heightOffset - width - hysteresis)) || toneholeRead[8] < senseDistance) {
        inTargetRegion = false;
    }

    halfHoleTargetRegionState[i] = inTargetRegion;
    if (((change < fingerRate) || (ED[preset][HALFHOLE_FINGERRATE] == 127) || ((pitchBendModeSelector[preset] == kPitchBendSlideVibrato || pitchBendModeSelector[preset] == kPitchBendLegatoSlideVibrato) && !ED[preset][HALFHOLE_USE_MIDI_NOTE])) && inTargetRegion) {  // Snap to semitone if the finger is moving slowly enough (or we're using slide) and it is within the defined region.
        snapped[i] = true;
    }

    if (!inTargetRegion) {
        snapped[i] = false;
        if (halfHoleShift[i] == true) {
            halfHoleShift[i] = false;
        }
    }

    if (snapped[i] == true) {
        if (!ED[preset][HALFHOLE_USE_MIDI_NOTE]) {

            iPitchBend[i] = pitchBendPerSemi;  // Snap to semitone if not using MIDI note instead.
        } else {
            halfHoleShift[i] = true;  // Or shift MIDI note.
        }
    }


    // Calculate slide here if we're not snapped to semitone. We calculate the slide in two portions, converging on the edges of the target region at one semitone. This gives a smooth transition from sliding to semitone.
    if (!snapped[i] && !inSlideHyst && !ED[preset][HALFHOLE_USE_MIDI_NOTE] && (pitchBendModeSelector[preset] == kPitchBendSlideVibrato || pitchBendModeSelector[preset] == kPitchBendLegatoSlideVibrato)) {
        if (toneholeRead[i] < (center - heightOffset)) {                                                                                                      // The sensor value is lower than the target region.
            float tempToneholeScale = (((16383.0f / midiBendRange)) / max((center - heightOffset - width) - toneholeBaseline[i] - senseDistance, 1) / 4.0f);  // We need to recalculate the tonehole scaling factor based on whether we are above the region or below it.
            iPitchBend[i] = ((((int)((toneholeRead[i] - senseDistance) * tempToneholeScale)) * -offsetSteps));
        } else {  // The sensor value is higher than the target region.
            float tempToneholeScale = (((16383.0f / midiBendRange)) / max(toneholeCovered[i] - (center - heightOffset + width), 1) / 4.0f);
            iPitchBend[i] = pitchBendPerSemi + ((((int)((toneholeRead[i] - (center - heightOffset + width)) * tempToneholeScale)) * -offsetSteps));
        }
    }
}











void calculateAndSendPitchbend() {

    bool pitchBendUsed = false;

    if (ED[preset][EXPRESSION_ON] && !switches[preset][BAGLESS]) {
        getExpression();  // If using pitchbend expression, calculate pitchbend based on pressure reading.
        pitchBendUsed = true;
    }
    if (IMUsettings[preset][MAP_ROLL_TO_PITCHBEND] || IMUsettings[preset][MAP_ELEVATION_TO_PITCHBEND] || IMUsettings[preset][MAP_YAW_TO_PITCHBEND]) {
        getIMUpitchbend();
        pitchBendUsed = true;
    }
    if (pitchBendMode != kPitchBendNone || ED[preset][HALFHOLE_PITCHBEND]) {
        if (!customEnabled) {
            handlePitchBend();
        } else {
            handleCustomPitchBend();
        }
        pitchBendUsed = true;
    }
    shakeForVibrato();  // This always needs to be called to detect the shake "button" gesture.
    if (IMUsettings[preset][Y_SHAKE_PITCHBEND] || IMUsettings[preset][Y_SHAKE_MOD_CC] || IMUsettings[preset][Y_SHAKE_MOD_CHPRESS] || IMUsettings[preset][Y_SHAKE_MOD_KEYPRESS]) {
        pitchBendUsed = true;
    }
    if (pitchBendUsed) {  // Send pitchbend if necessary.
        sendPitchbend();
    }
}










void sendPitchbend() {
    static int prevRawPitchBend = 0;

    pitchBend = 0;  // Reset the overall pitchbend in preparation for adding up the contributions from all the toneholes.
    for (byte i = 0; i < 9; i++) {
        pitchBend = pitchBend + iPitchBend[i];
    }

    bool halfholeUsingMidiNote = ED[preset][HALFHOLE_PITCHBEND] && ED[preset][HALFHOLE_USE_MIDI_NOTE];

    int noteshift = 0;
    if (noteon && pitchBendModeSelector[preset] == kPitchBendLegatoSlideVibrato && !halfholeUsingMidiNote) {
        noteshift = (notePlaying - shift) - newNote;
        pitchBend += (int)(noteshift * pitchBendPerSemi);

        // we are sending PB at a higher rate in this mode, so we can average the current with the last
        // to provide the smallest amount of smoothing to the raw note value which avoids artifacts
        // in some destination sound sources

        if (resetBendFilter) {  // don't average in this case (happens around a note on)
            prevRawPitchBend = pitchBend;
            resetBendFilter = false;
        } else {
            int avgbend = (prevRawPitchBend + pitchBend) >> 1;
            prevRawPitchBend = pitchBend;
            pitchBend = avgbend;
        }
    }

    pitchBend = 8192 - pitchBend + expression + shakeVibrato + IMUpitchbend;  // Add up all sources of pitchbend.

    if (pitchBend < 0) {
        pitchBend = 0;
    } else if (pitchBend > 16383) {
        pitchBend = 16383;
    }

    if (prevPitchBend != pitchBend) {
        if (noteon) {
            sendMIDI(PITCH_BEND, mainMidiChannel, pitchBend & 0x7F, pitchBend >> 7);
            prevPitchBend = pitchBend;
        }
    }
}










void sendNote() {
    const int velDelayMs = switches[preset][SEND_AFTERTOUCH] != 0 ? 3 : 16;

    bool halfHoleUsingMidiNote = ED[preset][HALFHOLE_PITCHBEND] && ED[preset][HALFHOLE_USE_MIDI_NOTE];
    int targetPlayedNote = newNote + shift;
    int currentPlayedNote = notePlaying;

    int legatoSlideLimit = midiBendRange;  // legato slide mode will ONLY retrigger a note if the bend range is exceeded, it handles its other features in getSlide()/sendPitchbend()

    if (  // Several conditions to tell if we need to turn on a new note.
      (!noteon
       || (pitchBendModeSelector[preset] != kPitchBendLegatoSlideVibrato && targetPlayedNote != currentPlayedNote)
       || (pitchBendModeSelector[preset] == kPitchBendLegatoSlideVibrato && halfHoleUsingMidiNote && targetPlayedNote != currentPlayedNote)
       || (pitchBendModeSelector[preset] == kPitchBendLegatoSlideVibrato && !halfHoleUsingMidiNote && abs(newNote - (notePlaying - shift)) >= legatoSlideLimit))
      && newNote != 0
      && ((newState > 1 && !switches[preset][BAGLESS]) || (switches[preset][BAGLESS] && play))
      && !(switches[preset][SEND_VELOCITY] && !noteon && ((millis() - velocityDelayTimer) < velDelayMs))) {
        int notewason = noteon;
        int notewasplaying = notePlaying;


        // If this is a fresh/tongued note calculate pressure now to get the freshest initial velocity/pressure
        if (!notewason) {
            if (ED[preset][SEND_PRESSURE]) {
                calculatePressure(0);
            }
            if (switches[preset][SEND_VELOCITY]) {
                calculatePressure(1);
            }
            if (switches[preset][SEND_AFTERTOUCH] & 1) {
                calculatePressure(2);
            }
            if (switches[preset][SEND_AFTERTOUCH] & 2) {
                calculatePressure(3);
            }

            if (IMUsettings[preset][AUTOCENTER_YAW] == true && (millis() - autoCenterYawTimer) > (IMUsettings[preset][AUTOCENTER_YAW_INTERVAL] * 250)) {  // Recenter yaw when we send a new note if there has been enough silence.
                centerIMU();
            }
        }


        if (notewason && !switches[preset][LEGATO]) {  // Send prior noteoff now if legato is selected.
            sendMIDI(NOTE_OFF, mainMidiChannel, notePlaying, 64);
            notewason = 0;
        }


        if (WARBL2settings[MIDI_DESTINATION] == 0 || connIntvl == 0) {                                                               // Only send here if not connected to BLE (to reduce jitter). I can't detect much difference, if any. (AM)
            if (ED[preset][SEND_PRESSURE] == 1 || switches[preset][SEND_AFTERTOUCH] != 0 || switches[preset][SEND_VELOCITY] == 1) {  // Need to send pressure prior to note, in case we are using it for velocity.
                sendPressure(true);
            }
        }

        // Set it now so that send pitchbend will operate correctly.
        noteon = 1;  // Keep track of the fact that there's a note turned on.
        notePlaying = newNote + shift;
        resetBendFilter = true;

        // Send pitch bend immediately prior to note if necessary.
        if (switches[preset][IMMEDIATE_PB]) {
            calculateAndSendPitchbend();
        }

        sendMIDI(NOTE_ON, mainMidiChannel, newNote + shift, velocity);  // Send the new note.

        if (notewason) {
            // Turn off the previous note after turning on the new one (if it wasn't already done above).
            // We do it after to signal to synths that the notes are legato (not all synths will respond to this).
            sendMIDI(NOTE_OFF, mainMidiChannel, notewasplaying, 64);
        }

        pitchBendTimer = millis();  // For some reason it sounds best if we don't send pitchbend right away after starting a new note.
        noteOnTimestamp = millis();
        powerDownTimer = pitchBendTimer;  // Reset the powerDown timer because we're actively sending notes.

        prevNote = newNote;

        if (ED[preset][DRONES_CONTROL_MODE] == 2 && !dronesOn) {  // Start drones if drones are being controlled with chanter on/off.
            startDrones();
        }
    }


    if (noteon) {  // Several conditions to turn a note off
        if (
          ((newState == SILENCE && !switches[preset][BAGLESS]) || newNote == 0 || (switches[preset][BAGLESS] && !play)) ||  // If the state drops to 1 (off) or we're in bagless mode and the sound has been turned off.
          (modeSelector[preset] == kModeNorthumbrian && newNote == 63) ||                                                   // Or closed Northumbrian pipe.
          (breathMode != kPressureBell && holeCovered == 0b111111111)) {                                                    // Or completely closed pipe with any fingering chart.
            sendMIDI(NOTE_OFF, mainMidiChannel, notePlaying, 64);                                                           // Turn the note off if the breath pressure drops or the bell sensor is covered and all the finger holes are covered.
                                                                                                                            // Keep track.

            if (IMUsettings[preset][AUTOCENTER_YAW] == true) {  // Reset the autocenter yaw timer.
                autoCenterYawTimer = millis();
            }

            // Not sure if this is necessary here because it won't have an effect if there's no note playing(?) (AM)
            //sendPressure(true);

            noteon = 0;

            if (ED[preset][DRONES_CONTROL_MODE] == 2 && dronesOn) {  // Stop drones if drones are being controlled with chanter on/off
                stopDrones();
            }
        }
    }
}










// Blink any LED according to blinkNumber[].
void blink() {

    static unsigned long ledTimer[3];

    for (byte i = 0; i < 3; i++) {
        if (blinkNumber[i] > 0) {
            if ((millis() - ledTimer[i]) >= 200) {
                ledTimer[i] = millis();

                if (LEDon[i]) {
                    analogWrite(LEDpins[i], 0);
                    blinkNumber[i]--;
                    LEDon[i] = 0;
                    return;
                }

                else {
                    analogWrite(LEDpins[i], 1023);
                    LEDon[i] = 1;
                }
            }
        }
    }
}










// Pulse LED with 10-bit sine wave.
void pulse() {

    static bool prevPulseState[] = { false, false, false };
    static float in[] = { 4.712f, 4.712f, 4.712f };
    float out[3];
    const float rate = 0.005f;  // Smaller constant makes pulse speed slower.


    for (byte i = 0; i < 3; i++) {
        if (pulseLED[i] == true) {
            prevPulseState[i] = true;
            in[i] = in[i] + rate;
            if (in[i] > 10.995f)
                in[i] = 4.712f;
            out[i] = sin(in[i]) * 511.5f + 511.5f;
            analogWrite(LEDpins[i], out[i]);
            in[i] = in[i] + rate * out[i] / 1023;  // Modify sine wave to spend less time at higher brightness (human eye can't detect changes in higher values as well).
        } else if (prevPulseState[i] == true) {
            prevPulseState[i] = false;
            analogWrite(LEDpins[i], 0);  // If pulsing was just turned off, write 0.
            in[i] = 4.712f;              // Reset so we'll start from 0 next time pulse is turned on.
        }
    }
}










//Incoming CC message from USB
void handleControlChangeFromUSB(byte channel, byte number, byte value) {
    handleControlChange(MIDI_SOURCE_USB, channel, number, value);
}


//Incoming PC message from USB
void handleProgramChangeFromUSB(byte channel, byte value) {
    handleProgramChange(MIDI_SOURCE_BLE, channel, value);
}


//Incoming CC message from BLE
void handleControlChangeFromBLE(byte channel, byte number, byte value) {
    handleControlChange(MIDI_SOURCE_BLE, channel, number, value);
}


//Incoming PC message from BLE
void handleProgramChangeFromBLE(byte channel, byte value) {
    handleProgramChange(MIDI_SOURCE_BLE, channel, value);
}









// Handle incoming program messages.
void handleProgramChange(byte source, byte channel, byte value) {

    // Listen to all channels for now.
    //if (channel == mainMidiChannel) {  // If the received PC is on the same channel that WARBL is sending on,
    if (value < 3) {
        preset = value;  // change the preset.
        play = 0;
        loadPrefs();  // Load the correct user settings based on current preset.
        blinkNumber[GREEN_LED] = abs(preset) + 1;
        if (communicationMode) {
            sendSettings();  // Tell communications tool to switch preset and send all settings for current preset.
        }
    }
    //}
}










// Handle incoming CC messages from the Configuration Tool.
void handleControlChange(byte source, byte channel, byte number, byte value) {
    //Serial.println(channel);
    //Serial.println(number);
    //Serial.println(value);
    //Serial.println("");

    if (number < 120) {  // Chrome sends CC 121 and 123 on all channels when it connects, so ignore these.

        if ((channel) == MIDI_CONFIG_TOOL_CHANNEL) {  // If we're on channel 7, we may be receiving messages from the configuration tool.
            powerDownTimer = millis();                // Reset the powerDown timer because we've heard from the Config Tool.
            blinkNumber[GREEN_LED] = 1;               // Blink once, indicating a received message. Some commands below will change this to three (or zero) blinks.


            /////// CC 102
            if (number == MIDI_CC_102) {                                               // Many settings are controlled by a value in CC 102 (always channel 7).
                if (value >= MIDI_CALIB_MSGS_START && value <= MIDI_CALIB_MSGS_END) {  // Handle sensor calibration commands from the configuration tool.
                    int hindex = (value >> 1) - 1;
                    if ((value & 1) == 0) {
                        toneholeCovered[hindex] -= 5;
                        if ((toneholeCovered[hindex] - toneholeBaseline[hindex] - 4) < 5) {  // If the tonehole calibration gets set too low so that it would never register as being uncovered, send a message to the configuration tool.
                            sendMIDI(MIDI_CC_102_MSG, (MIDI_MAX_CALIB_MSGS_START + (hindex)));
                        }
                    } else {
                        toneholeCovered[((value + 1) >> 1) - 1] += 5;
                    }
                }

                if (value == MIDI_SAVE_CALIB) {  // Save calibration if directed.
                    saveCalibration();
                    blinkNumber[GREEN_LED] = 3;
                }

                else if (value == MIDI_START_CALIB) {  // Begin auto-calibration if directed.
                    blinkNumber[GREEN_LED] = 0;
                    calibration = 1;
                }

                else if (value == MIDI_ENTER_COMM_MODE) {  // When communication is established, send all current settings to tool.
                    diagnosticMode = 0;                    // Keep Config Tool mode and diagnostic mode mutually exclusive.
                    diagnosticModeSource = MIDI_SOURCE_NONE;
                    communicationMode = 1;
                    communicationModeSource = source;


#if DEBUG_CONFIG_TOOL
                    Serial.print("Entering CommMode from ");
                    Serial.println(communicationModeSource);
#endif
                    sendSettings();
                }

                else if (value == MIDI_EXIT_COMM_MODE) {  // Turn off communication mode.
                    //If comm mode was activated on the same source, it turns it off
                    if (communicationModeSource == source) {
                        communicationMode = 0;
                        communicationModeSource = MIDI_SOURCE_NONE;
                    }
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
