amowry/WARBL2/warbl2_firmware/ATmega_programming.ino

// Reprogram the ATmega32u4 if necessary.
// Modified from the Adafruit_AVRProg library.
// LED will flash teal 3 times to indicate success.
// To use, paste in the ATmega firmware hex file below, make sure HEX_SIZE is set large enough (otherwise it won't compile), and set the new ATmega firmware version in Defines.h so we know the ATmega will need to be programmed.

#define HEX_SIZE 20000  // This needs to be set larger than the size of the hex file in bytes. If it is larger than necessary the buffer will take up unneeded space in flash.

#define FUSE_PROT 0               // Memory protection
#define FUSE_LOW 1                // Low fuse
#define FUSE_HIGH 2               // High fuse
#define FUSE_EXT 3                // Extended fuse
#define FUSE_CLOCKSPEED 10000     // Fuses need to be programmed slowly.
#define FLASH_CLOCKSPEED 1000000  // Once fused you can flash fast!
#define AVRPROG_RESET 26          // This pin is left in default state (highZ) when not programming (it has a pullup resistor).
#define debug(string)             // Serial.println(string);


typedef struct image {             // Struct for holding program fuses & code
    uint16_t image_chipsig;        // Low two bytes of signature
    byte image_progfuses[10];      // Fuses to set during programming (e.g unlock)
    byte image_normfuses[10];      // Fuses to set after programming (e.g lock)
    byte fusemask[10];             // Not all bits are used in the fuses, mask the ones we do use.
    uint16_t chipsize;             // Total size for flash programming, in bytes.
    byte image_pagesize;           // Page size for flash programming, in bytes.
    byte image_hexcode[HEX_SIZE];  // Max buffer for intel hex format image (text)
} image_t;

static byte pageBuffer[8 * 1024];  // Megabuff
extern const image_t *images[];

// The firmware hex file to flash. Paste it in between the start and end markers {R"( and )"}.
const image_t PROGMEM image_32u4_boot = { 0x9587, { 0x3F, 0xFF, 0xD8, 0x0B }, { 0x2F, 0xFF, 0xD9, 0x0B }, { 0x3F, 0xFF, 0xFF, 0x0F }, 32768, 128,  // Signature, programming fuses, final fuses, fuse verify mask, flash size, page size
                                          { R"(
:100000000C94DD000C94EF060C94C8060C94A10629
:100010000C947A060C9405010C9405010C9453067B
:100020000C9405010C9405010C945E030C94C70319
:100030000C9405010C9405010C9405010C94050128
:100040000C9405010C9405010C9405010C94050118
:100050000C9405010C9405010C9405010C940906FF
:100060000C9417070C9405010C9405010C940501E0
:100070000C9405010C9416070C9405010C940501D1
:100080000C9405010C9405010C9405010C940501D8
:100090000C9405010C9405010C9405010C940501C8
:1000A0000C9405010C9405010C9405010706050448
:1000B0000100080A0B0C0D090000000025002800B3
:1000C0002B002E00310000000000240027002A0031
:1000D0002D003000000000002300260029002C0025
:1000E0002F000404040404030405020202020403B2
:1000F00002020202060606060606040402020204C2
:100100000404080201104080401020408040800814
:100110000204018040201002011080102040402085
:100120000000000200090F0000030401000C0000A1
:1001300000000000000000000000000000000008B7
:100140000B0002020200000904000001020200008C
:1001500005240010010524010101042402060524E0
:100160000600010705810310004009040100020A8E
:10017000000000070502024000000705830240005E
:10018000000403090412010002EF020140D80487B1
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
    }

    for (byte i = 0; i < 3; i++) {  // Indicate success.
        analogWrite(LEDpins[GREEN_LED], 1023);
        analogWrite(LEDpins[BLUE_LED], 1023);
        delay(200);
        analogWrite(LEDpins[GREEN_LED], 0);
        analogWrite(LEDpins[BLUE_LED], 0);
        delay(200);
    }

    return true;  // Success
}




void endProgramMode(void) {
    SPI.endTransaction();
    digitalWrite(AVRPROG_RESET, LOW);
    pinMode(AVRPROG_RESET, INPUT);
}


bool targetPower(bool poweron) {
    if (poweron) {
        Serial.print(F("Starting Program Mode..."));
        if (startProgramMode(100000)) {
            Serial.println(F(" [OK]"));
            return true;
        } else {
            Serial.println(F(" [FAIL]"));
            return false;
        }
    } else {
        endProgramMode();
        return true;
    }
}


bool startProgramMode(uint32_t clockspeed) {
    pinMode(AVRPROG_RESET, OUTPUT);
    digitalWrite(AVRPROG_RESET, HIGH);
    delay(5);
    SPI.beginTransaction(SPISettings(clockspeed, MSBFIRST, SPI_MODE0));
    debug("...spi_init done");
    digitalWrite(AVRPROG_RESET, LOW);
    debug("...isp_transaction");
    uint16_t reply = isp_transaction(0xAC, 0x53, 0x00, 0x00);
    if (reply == 0x5300) {
        debug("...Done");
        return true;
    }
    Serial.print(reply, HEX);
    return false;
}


uint16_t readSignature(void) {
    startProgramMode(FUSE_CLOCKSPEED);
    uint16_t target_type = 0;
    target_type = isp_transaction(0x30, 0x00, 0x01, 0x00);
    target_type <<= 8;
    target_type |= isp_transaction(0x30, 0x00, 0x02, 0x00);
    endProgramMode();
    return target_type;
}


bool eraseChip(void) {
    startProgramMode(FUSE_CLOCKSPEED);
    if ((isp_transaction(0xAC, 0x80, 0, 0) & 0xFFFF) != 0x8000) {  // chip erase
        error(F("Error on chip erase command"));
    }
    busyWait();
    endProgramMode();
    return true;
}


bool programFuses(const byte *fuses, uint8_t num_fuses) {
    startProgramMode(FUSE_CLOCKSPEED);
    byte f;
    Serial.println(F("\nSetting fuses"));

    f = pgm_read_byte(&fuses[FUSE_PROT]);
    if (f) {
        Serial.print(F("\tSet Lock Fuse to: "));
        Serial.println(f, HEX);
        if ((isp_transaction(0xAC, 0xE0, 0x00, f) & 0xFFFF) != 0xE000) {
            return false;
        }
    }
    busyWait();
    f = pgm_read_byte(&fuses[FUSE_LOW]);
    if (f) {
        Serial.print(F("\tSet Low Fuse to: "));
        Serial.println(f, HEX);
        if ((isp_transaction(0xAC, 0xA0, 0x00, f) & 0xFFFF) != 0xA000) {
            return false;
        }
    }
    busyWait();
    f = pgm_read_byte(&fuses[FUSE_HIGH]);
    if (f) {
        Serial.print(F("\tSet High Fuse to: "));
        Serial.println(f, HEX);
        if ((isp_transaction(0xAC, 0xA8, 0x00, f) & 0xFFFF) != 0xA800) {
            return false;
        }
    }
    busyWait();
    f = pgm_read_byte(&fuses[FUSE_EXT]);
    if (f) {
        Serial.print(F("\tSet Ext Fuse to: "));
        Serial.println(f, HEX);
        if ((isp_transaction(0xAC, 0xA4, 0x00, f) & 0xFFFF) != 0xA400) {
            return false;
        }
    }
    busyWait();
    Serial.println();
    endProgramMode();
    return true;
}


bool verifyFuses(const byte *fuses, const byte *fusemask) {
    startProgramMode(FUSE_CLOCKSPEED);
    byte f;
    Serial.println(F("Verifying fuses..."));
    f = pgm_read_byte(&fuses[FUSE_PROT]);
    if (f) {
        uint8_t readfuse = isp_transaction(0x58, 0x00, 0x00, 0x00);  // lock fuse
        readfuse &= pgm_read_byte(&fusemask[FUSE_PROT]);
        Serial.print(F("\tLock Fuse = 0x"));
        Serial.println(readfuse, HEX);
        if (readfuse != f)
            return false;
    }
    f = pgm_read_byte(&fuses[FUSE_LOW]);
    if (f) {
        uint8_t readfuse = isp_transaction(0x50, 0x00, 0x00, 0x00);  // low fuse
        Serial.print(F("\tLow Fuse = 0x"));
        Serial.println(readfuse, HEX);
        readfuse &= pgm_read_byte(&fusemask[FUSE_LOW]);
        if (readfuse != f)
            return false;
    }
    f = pgm_read_byte(&fuses[FUSE_HIGH]);
    if (f) {
        uint8_t readfuse = isp_transaction(0x58, 0x08, 0x00, 0x00);  // high fuse
        readfuse &= pgm_read_byte(&fusemask[FUSE_HIGH]);
        Serial.print(F("\tHigh Fuse = 0x"));
        Serial.println(readfuse, HEX);
        if (readfuse != f)
            return false;
    }
    f = pgm_read_byte(&fuses[FUSE_EXT]);
    if (f) {
        uint8_t readfuse = isp_transaction(0x50, 0x08, 0x00, 0x00);  // ext fuse
        readfuse &= pgm_read_byte(&fusemask[FUSE_EXT]);
        Serial.print(F("\tExt Fuse = 0x"));
        Serial.println(readfuse, HEX);
        if (readfuse != f)
            return false;
    }
    Serial.println();
    endProgramMode();
    return true;
}


bool writeImage(const byte *hextext, uint32_t pagesize, uint32_t chipsize) {
    uint32_t flash_start = 0;
    uint32_t pageaddr = 0;

    while (pageaddr < chipsize && hextext) {
        const byte *hextextpos =
          readImagePage(hextext, pageaddr, pagesize, pageBuffer);

        bool blankpage = true;
        for (uint16_t i = 0; i < pagesize; i++) {
            if (pageBuffer[i] != 0xFF)
                blankpage = false;
        }
        if (!blankpage) {
            if (!flashPage(pageBuffer, flash_start + pageaddr, pagesize))
                return false;
        }
        hextext = hextextpos;
        pageaddr += pagesize;
    }
    return true;
}


const byte *readImagePage(const byte *hextext,
                          uint16_t pageaddr,
                          uint16_t pagesize,
                          byte *page) {
    const byte *beginning = hextext;

    // Fill page with erased state
    for (uint16_t i = 0; i < pagesize; i++) {
        page[i] = 0xFF;
    }

    while (1) {
        uint16_t len;
        uint16_t lineaddr;
        byte rectype;
        byte b, cksum = 0;
        char c;

        // Skip blank lines / CRLF leftovers
        do {
            c = pgm_read_byte(hextext++);
            if (c == 0) {
                return nullptr;
            }
        } while (c == '\n' || c == '\r');

        if (c != ':') {
            error(F("No colon?"));
            return nullptr;
        }

        // Byte count
        len = hexToByte(pgm_read_byte(hextext++));
        len = (len << 4) + hexToByte(pgm_read_byte(hextext++));
        cksum = len;

        // Address high
        b = hexToByte(pgm_read_byte(hextext++));
        b = (b << 4) + hexToByte(pgm_read_byte(hextext++));
        cksum += b;
        lineaddr = b << 8;

        // Address low
        b = hexToByte(pgm_read_byte(hextext++));
        b = (b << 4) + hexToByte(pgm_read_byte(hextext++));
        cksum += b;
        lineaddr |= b;

        // Record type
        rectype = hexToByte(pgm_read_byte(hextext++));
        rectype = (rectype << 4) + hexToByte(pgm_read_byte(hextext++));
        cksum += rectype;

        if (rectype == 0x01) {
            // EOF
            // consume checksum
            b = hexToByte(pgm_read_byte(hextext++));
            b = (b << 4) + hexToByte(pgm_read_byte(hextext++));
            cksum += b;

            // optional newline handling
            char eol = pgm_read_byte(hextext);
            if (eol == '\r' || eol == '\n') {
                hextext++;
            }

            if (cksum != 0) {
                error(F("Bad checksum at EOF"));
            }

            return nullptr;
        }

        if (rectype != 0x00) {
            // Unsupported non-data record: skip it cleanly
            for (uint16_t i = 0; i < len; i++) {
                b = hexToByte(pgm_read_byte(hextext++));
                b = (b << 4) + hexToByte(pgm_read_byte(hextext++));
                cksum += b;
            }

            b = hexToByte(pgm_read_byte(hextext++));
            b = (b << 4) + hexToByte(pgm_read_byte(hextext++));
            cksum += b;

            if (cksum != 0) {
                error(F("Bad checksum in non-data record"));
            }

            // eat newline(s)
            char eol = pgm_read_byte(hextext);
            if (eol == '\r') hextext++;
            if (pgm_read_byte(hextext) == '\n') hextext++;

            continue;
        }

        // If this record starts after this page, stop and let the caller
        // retry it on the next page.
        if (lineaddr >= (pageaddr + pagesize)) {
            return beginning;
        }

        // Read data bytes into the correct offset within the page
        for (uint16_t i = 0; i < len; i++) {
            b = hexToByte(pgm_read_byte(hextext++));
            b = (b << 4) + hexToByte(pgm_read_byte(hextext++));
            cksum += b;

            uint16_t absoluteAddr = lineaddr + i;

            if (absoluteAddr >= pageaddr && absoluteAddr < (pageaddr + pagesize)) {
                uint16_t offset = absoluteAddr - pageaddr;
                page[offset] = b;
            }
        }

        // Record checksum
        b = hexToByte(pgm_read_byte(hextext++));
        b = (b << 4) + hexToByte(pgm_read_byte(hextext++));
        cksum += b;

        if (cksum != 0) {
            error(F("Bad checksum in data record"));
        }

        // Eat CR/LF
        if (pgm_read_byte(hextext) == '\r') hextext++;
        if (pgm_read_byte(hextext) == '\n') hextext++;

        // Update "beginning" so next record becomes the retry point
        beginning = hextext;
    }
}


bool verifyImage(const byte *hextext) {
    startProgramMode(FLASH_CLOCKSPEED);  // start at 1MHz speed
    uint16_t len;
    byte b, cksum = 0;

    while (1) {
        uint16_t lineaddr;
        // read one line!
        char c = pgm_read_byte(hextext++);
        if (c == '\n' || c == '\r') {
            continue;
        }
        if (c != ':') {
            Serial.print(c);
            error(F(" No colon?"));
            break;
        }
        len = hexToByte(pgm_read_byte(hextext++));
        len = (len << 4) + hexToByte(pgm_read_byte(hextext++));
        cksum = len;

        b = hexToByte(pgm_read_byte(hextext++));  // record type
        b = (b << 4) + hexToByte(pgm_read_byte(hextext++));
        cksum += b;
        lineaddr = b;
        b = hexToByte(pgm_read_byte(hextext++));  // record type
        b = (b << 4) + hexToByte(pgm_read_byte(hextext++));
        cksum += b;
        lineaddr = (lineaddr << 8) + b;

        b = hexToByte(pgm_read_byte(hextext++));  // record type
        b = (b << 4) + hexToByte(pgm_read_byte(hextext++));
        cksum += b;

        if (b == 0x1) {
            // end record!
            break;
        }

        for (byte i = 0; i < len; i++) {
            // read 'n' bytes
            b = hexToByte(pgm_read_byte(hextext++));
            b = (b << 4) + hexToByte(pgm_read_byte(hextext++));
            cksum += b;

            // verify this byte!
            byte reply;
            if (lineaddr % 2) {  // for 'high' bytes
                reply = isp_transaction(0x28, lineaddr >> 9, lineaddr / 2, 0) & 0xFF;
            } else {  // for 'low' bytes
                reply = isp_transaction(0x20, lineaddr >> 9, lineaddr / 2, 0) & 0xFF;
            }
            if (b != reply) {
                Serial.println();
                Serial.print(F("Verification error at address 0x"));
                Serial.print(lineaddr, HEX);
                Serial.print(F(" Should be 0x"));
                Serial.print(b, HEX);
                Serial.print(F(" not 0x"));
                Serial.println(reply, HEX);
                return false;
            }
            lineaddr++;
        }

        b = hexToByte(pgm_read_byte(hextext++));  // chxsum
        b = (b << 4) + hexToByte(pgm_read_byte(hextext++));
        cksum += b;
        if (cksum != 0) {
            Serial.print(cksum, HEX);
            error(F(" - bad checksum"));
        }
        if (pgm_read_byte(hextext++) != '\n') {
            error(F("No end of line"));
        }
    }

    endProgramMode();
    return true;
}


bool flashWord(uint8_t hilo, uint16_t addr, uint8_t data) {
    if (isp_transaction(0x40 + 8 * hilo, addr >> 8 & 0xFF, addr & 0xFF, data) != addr) {
        return false;
    }
    return true;
}


bool flashPage(byte *pagebuff, uint16_t pageaddr,
               uint16_t pagesize) {
    Serial.print(F("Flashing page "));
    Serial.println(pageaddr, HEX);

    if (millis() - WDDTelapsedTime > 1000) {
        WDDTelapsedTime = millis();
        watchdogReset();  // Feed the watchdog.
        Serial.print(F("WDT reset"));
    }

    startProgramMode(FLASH_CLOCKSPEED);

    for (uint16_t i = 0; i < pagesize / 2; i++) {
        if (!flashWord(LOW, i, pagebuff[2 * i]))
            return false;
        if (!flashWord(HIGH, i, pagebuff[2 * i + 1]))
            return false;
    }

    pageaddr /= 2;

    uint16_t commitreply =
      isp_transaction(0x4C, (pageaddr >> 8) & 0xFF, pageaddr & 0xFF, 0);

    Serial.print(F("  Commit Page: 0x"));
    Serial.print(pageaddr, HEX);
    Serial.print(F(" -> 0x"));
    Serial.println(commitreply, HEX);
    if (commitreply != pageaddr)
        return false;

    busyWait();
    endProgramMode();
    return true;
}


void busyWait(void) {
    byte busybit;
    do {
        busybit = isp_transaction(0xF0, 0x0, 0x0, 0x0);
    } while (busybit & 0x01);
}


uint32_t isp_transaction(uint8_t a, uint8_t b, uint8_t c,
                         uint8_t d) {
    uint8_t l, n, m, o;
    (void)o;  // avoid unused var warning
    (void)m;  // avoid unused var warning
    (void)n;  // avoid unused var warning
    o = transfer(a);
    n = transfer(b);
    // if (n != a) error = -1;
    m = transfer(c);
    l = transfer(d);
    return ((m << 8) + l);
}


uint8_t transfer(uint8_t out) {
    return SPI.transfer(out);
}


byte hexToByte(byte h) {
    if (h >= '0' && h <= '9')
        return (h - '0');
    if (h >= 'A' && h <= 'F')
        return ((h - 'A') + 10);
    if (h >= 'a' && h <= 'f')
        return ((h - 'a') + 10);
    Serial.print("Read odd char 0x");
    Serial.print(h, HEX);
    Serial.println();
    error(F("Bad hex digit!"));
    return -1;
}


void error(const char *string) {
    Serial.println(string);
    while (1) {
    }
}


void error(const __FlashStringHelper *string) {
    Serial.println(string);
    while (1) {
    }
}
